ednspace/PyroLogger/Hardware/ds2760/ds2760/board.png

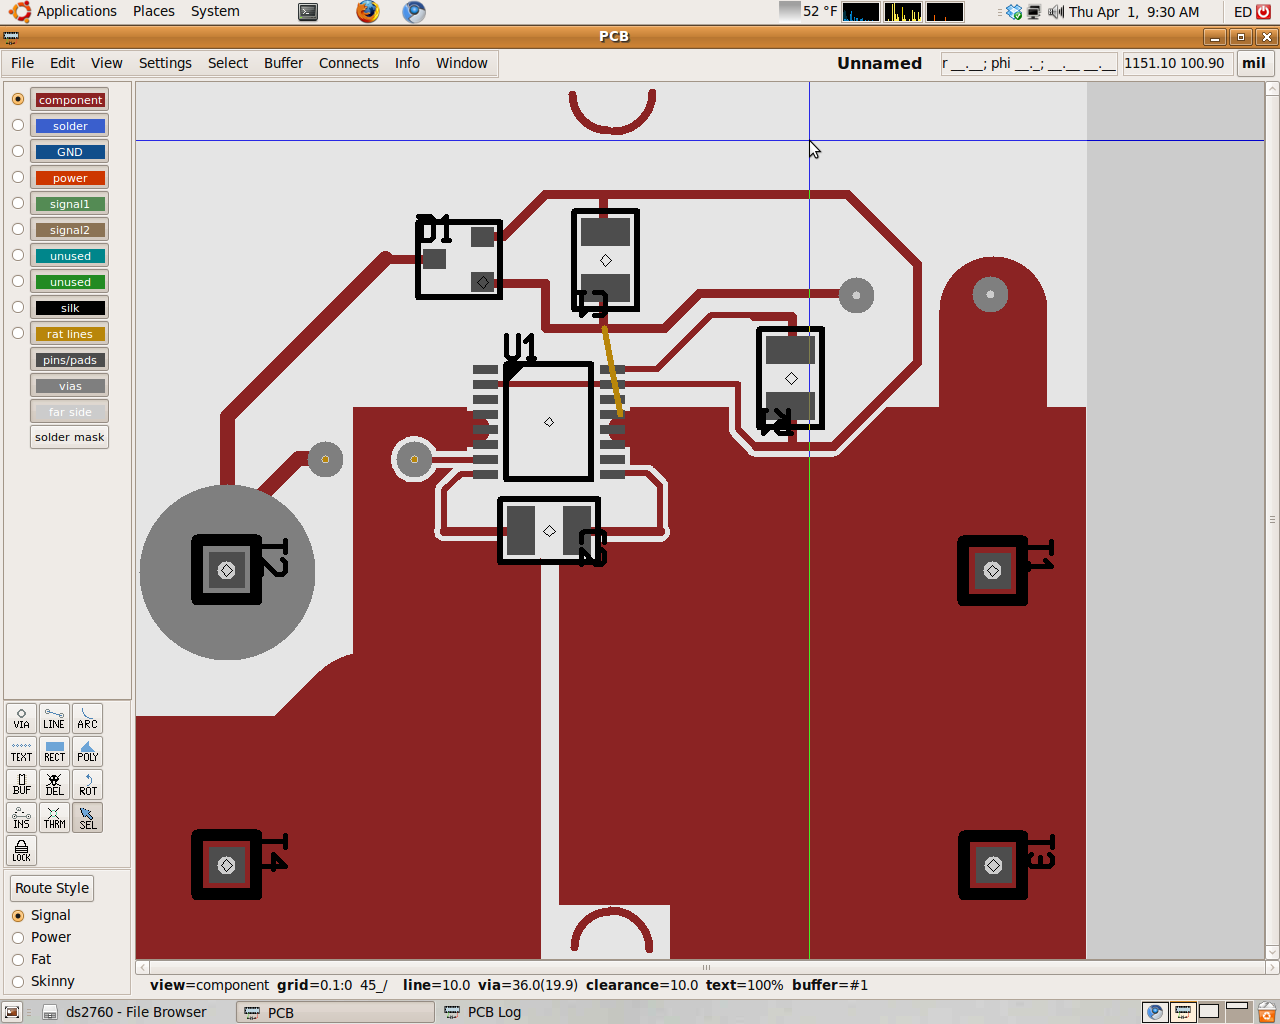
Hardware/ds2760/ds2760/board.png
