ednspace/PyroLogger/Hardware/FakeThermocouple/fake_scheme.JPG

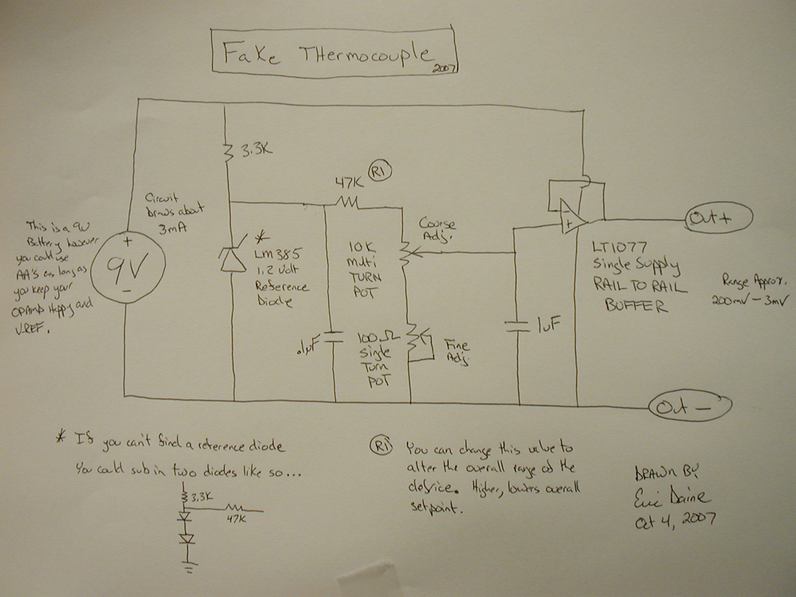
Hardware/FakeThermocouple/fake_scheme.JPG
