ednspace/PyroLogger/Images/2015-05-17 10.12.58.jpg

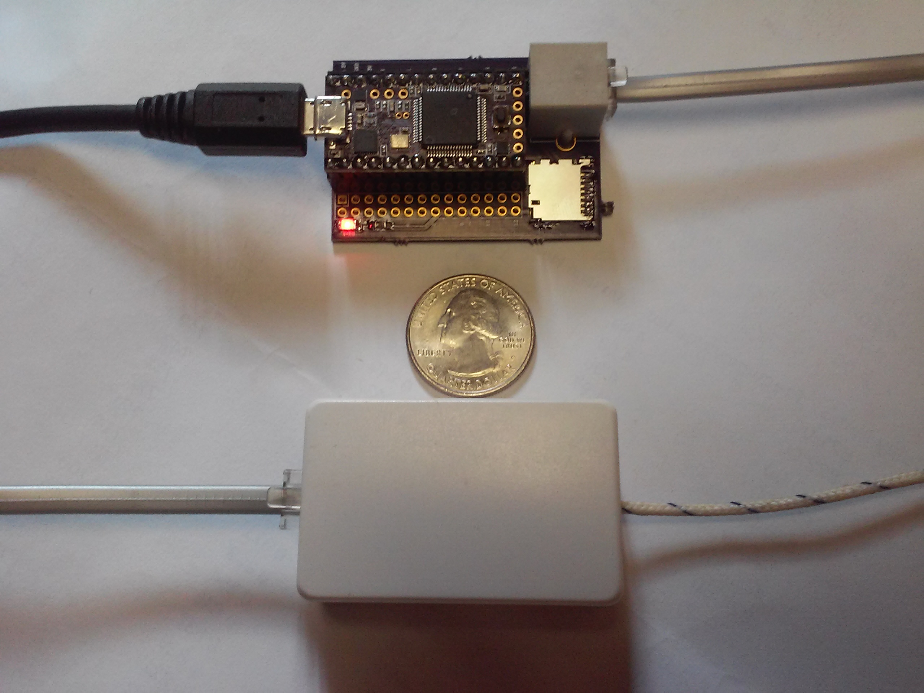
Images/2015-05-17 10.12.58.jpg
