ednspace/PyroLogger/Research/16F688_FT232RL.png

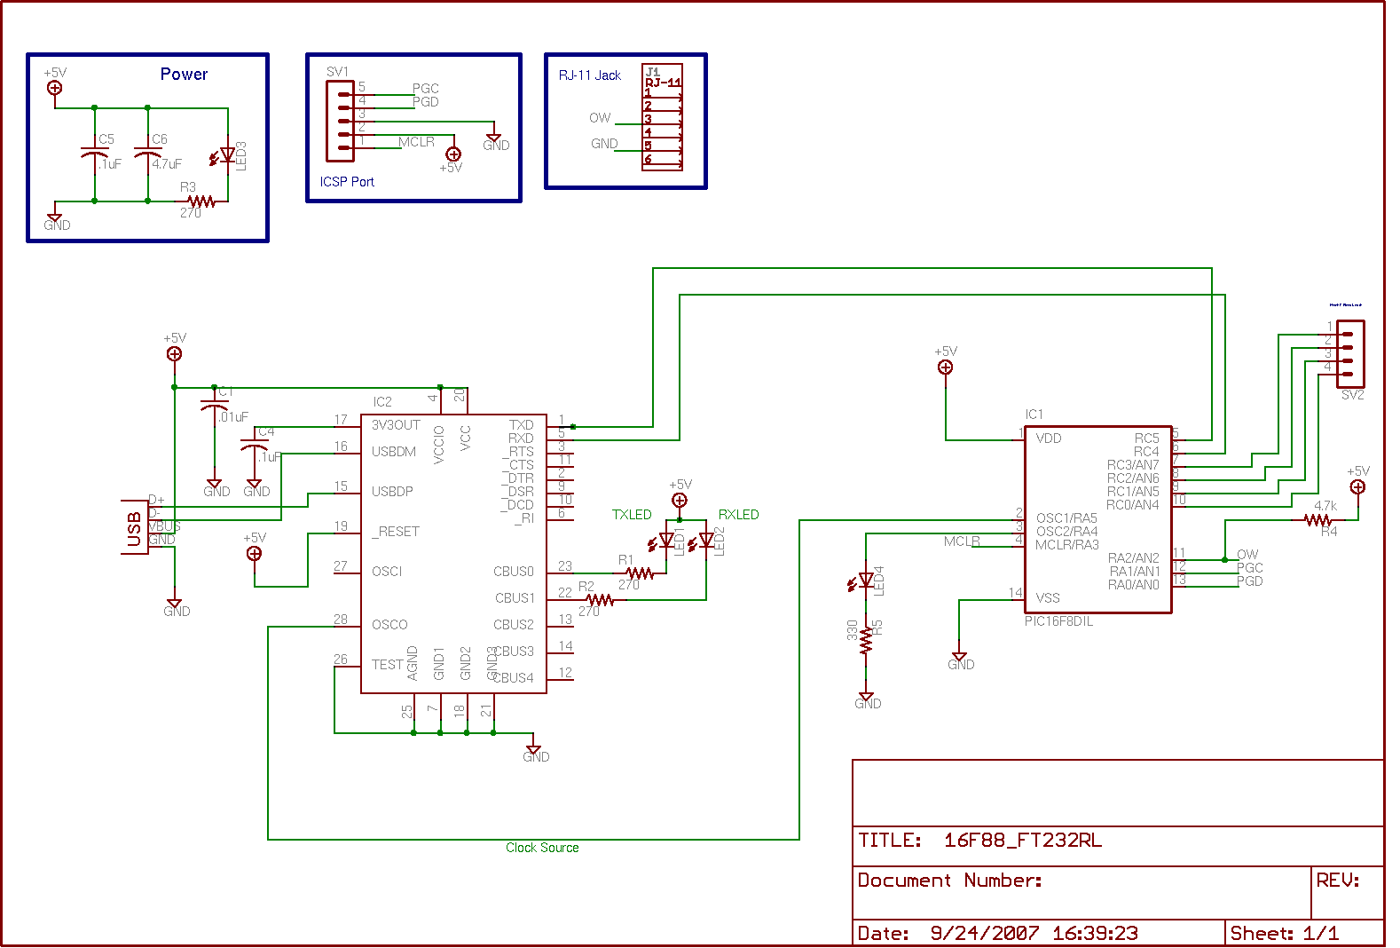
Research/16F688_FT232RL.png
