ednspace/PyroLogger/Research/ds2460.png

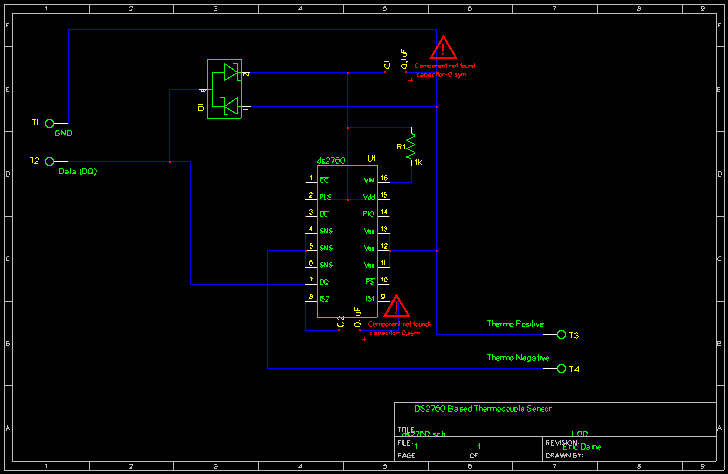
Research/ds2460.png
