ednspace/PyroLogger/Testing/Anagama_2006_oct/oct06.png

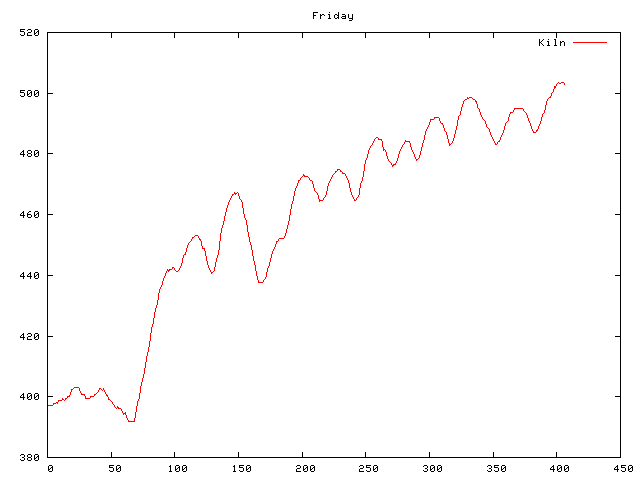
Testing/Anagama_2006_oct/oct06.png
