ednspace/PyroLogger/Testing/Anagama_2006_oct/oct07.png

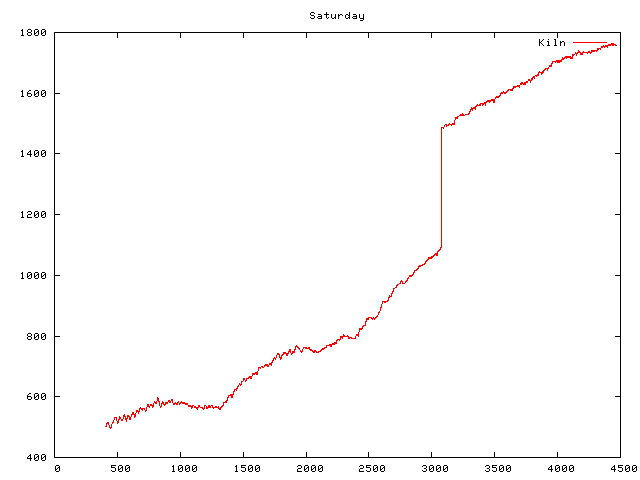
Testing/Anagama_2006_oct/oct07.png
