ednspace/PyroLogger/Testing/Anagama_2006_oct/oct08.png

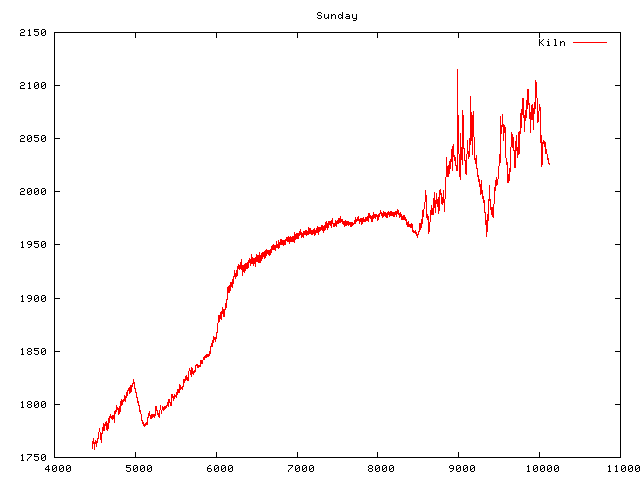
Testing/Anagama_2006_oct/oct08.png
