ednspace/PyroLogger/Testing/Anagama_2006_oct/oct09.png

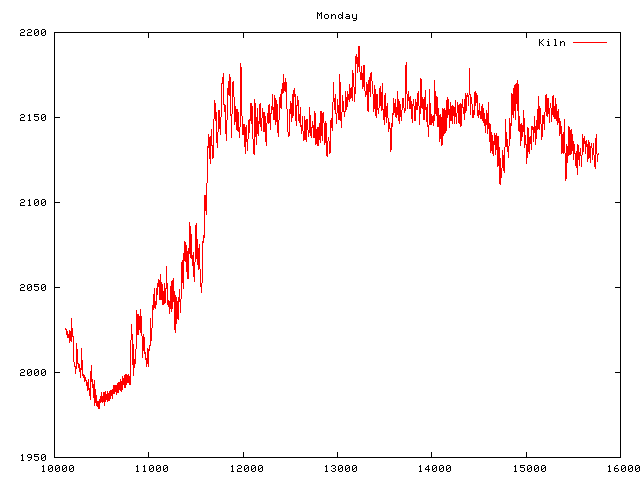
Testing/Anagama_2006_oct/oct09.png
