ednspace/PyroLogger/Testing/Anagama_2006_oct/oct10.png

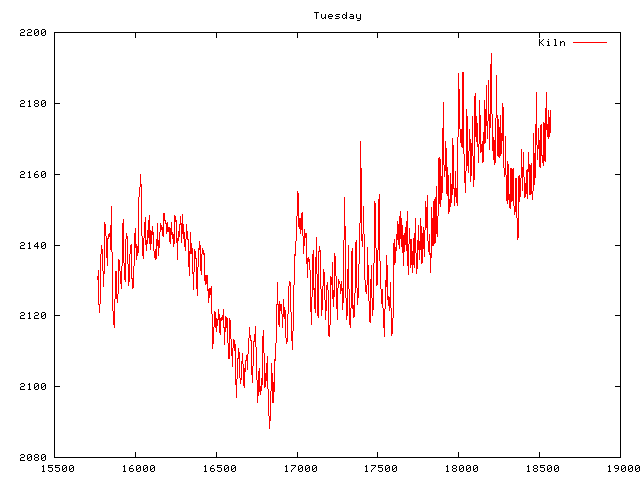
Testing/Anagama_2006_oct/oct10.png
