ednspace/PyroLogger/Testing/Anagama_2006_oct/Thumbs/whole.png

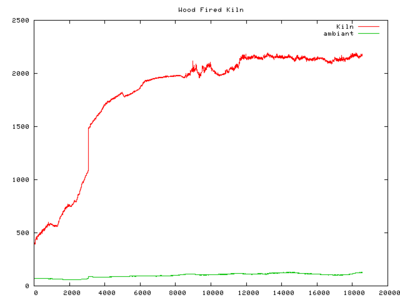
Testing/Anagama_2006_oct/Thumbs/whole.png
