ednspace/PyroLogger/Testing/Anagama_2007_march/march06.png

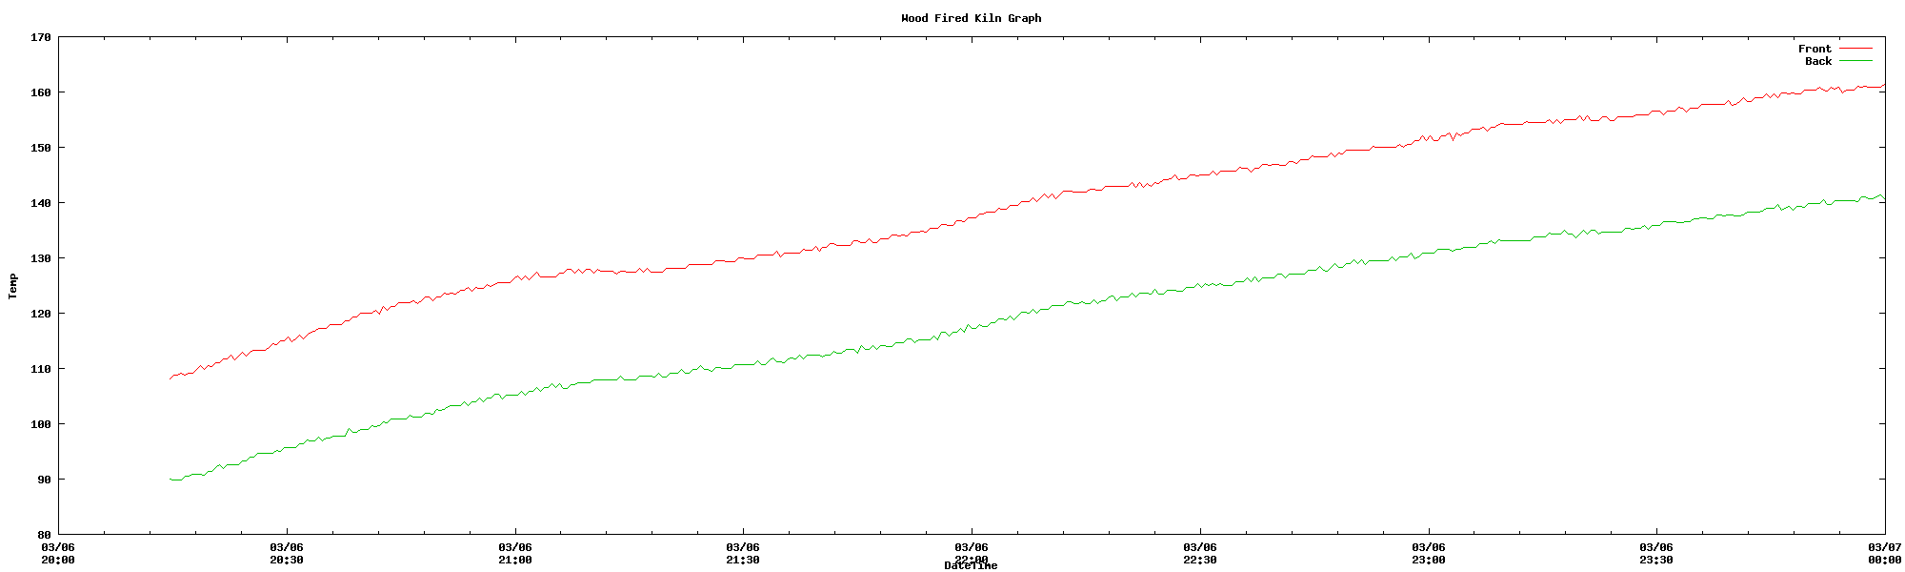
Testing/Anagama_2007_march/march06.png
