ednspace/PyroLogger/Testing/Anagama_2007_march/march07.png

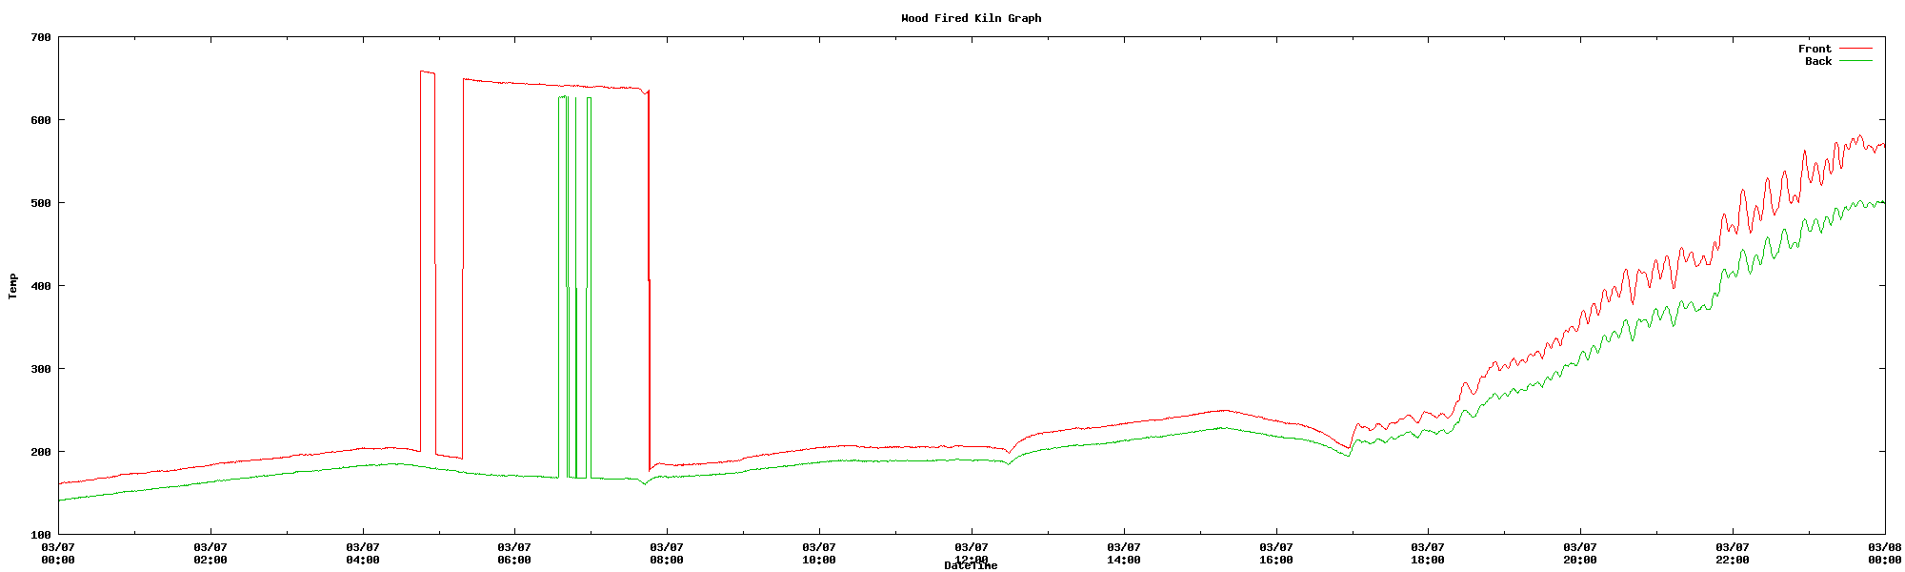
Testing/Anagama_2007_march/march07.png
