ednspace/PyroLogger/Testing/Anagama_2007_march/march08.png

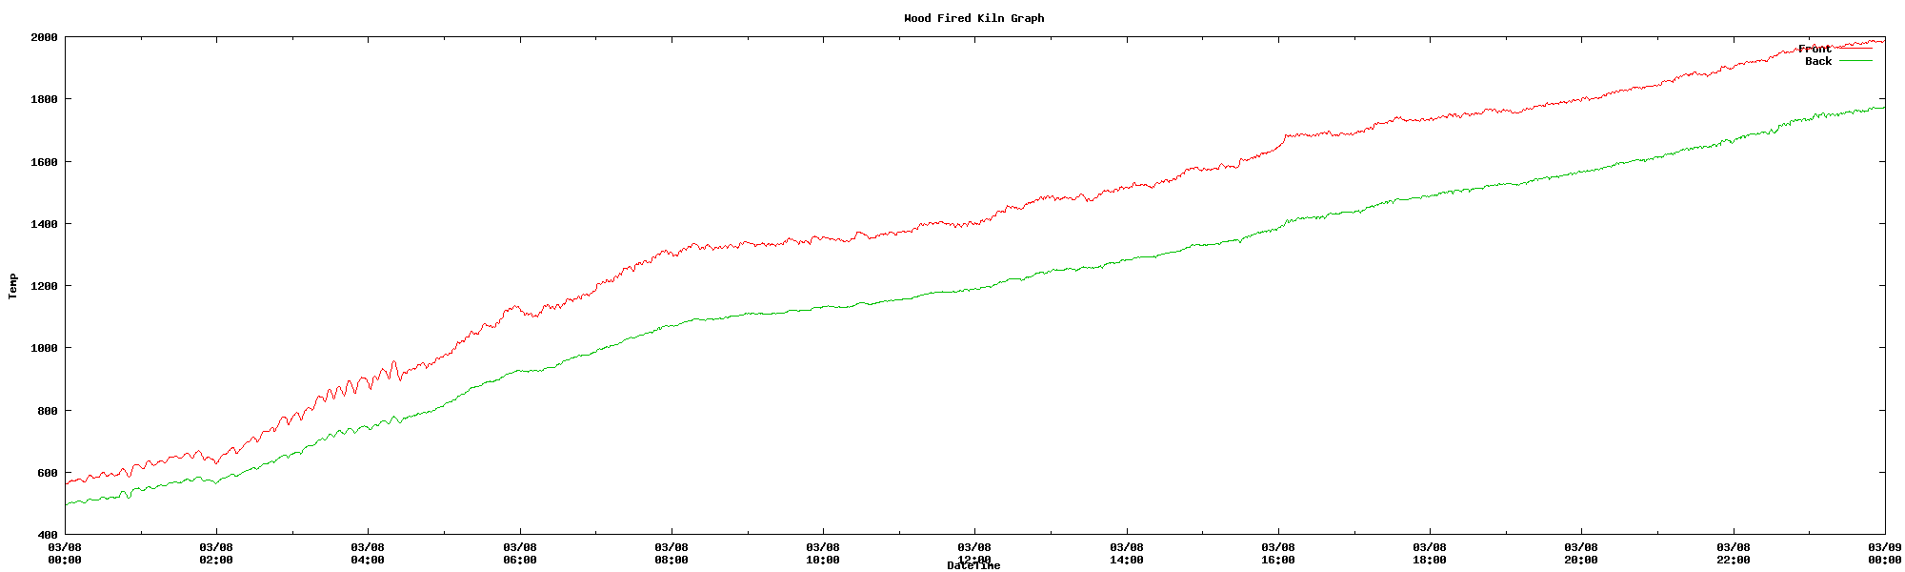
Testing/Anagama_2007_march/march08.png
