ednspace/PyroLogger/Testing/Anagama_2007_march/march09.png

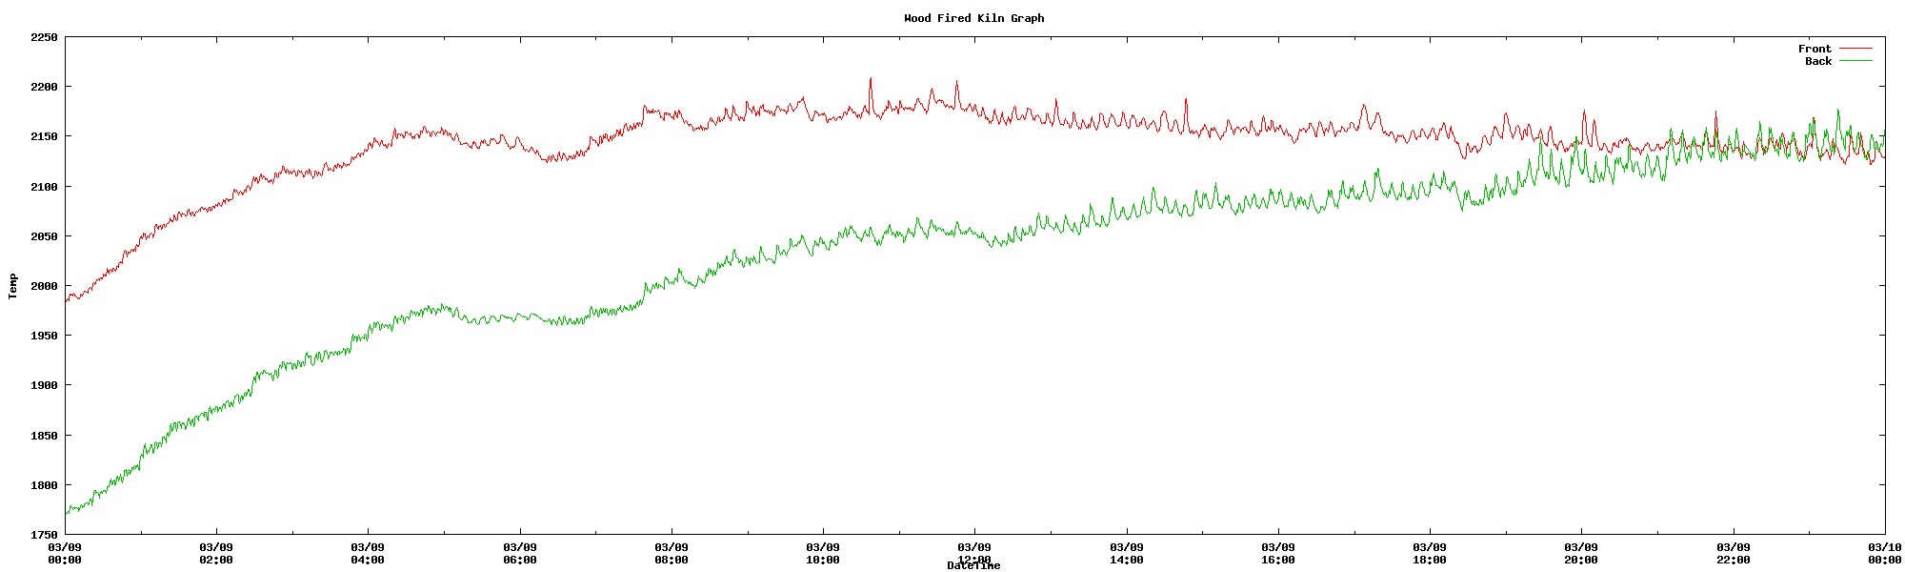
Testing/Anagama_2007_march/march09.png
