ednspace/PyroLogger/Testing/Anagama_2007_march/march10.png

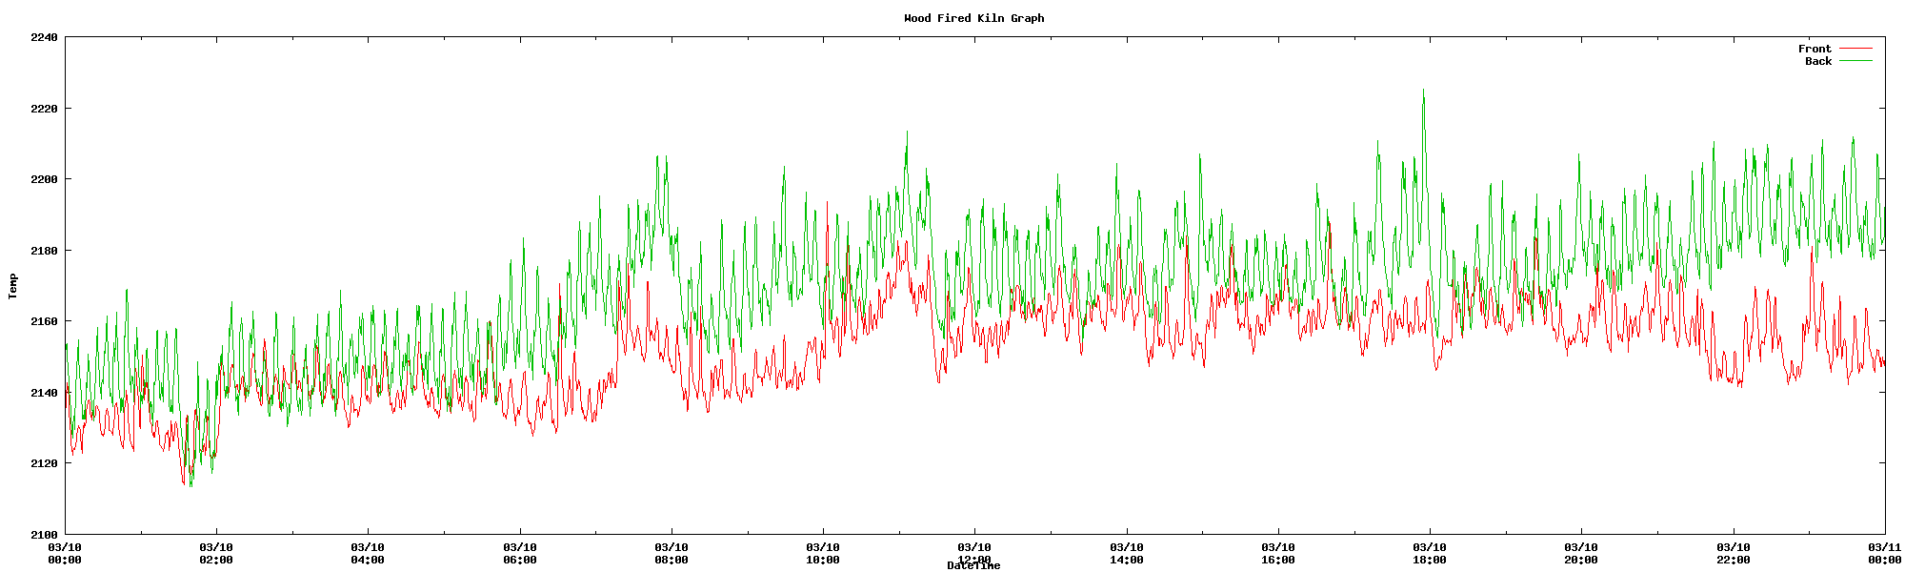
Testing/Anagama_2007_march/march10.png
