ednspace/PyroLogger/Testing/Anagama_2007_march/march11.png

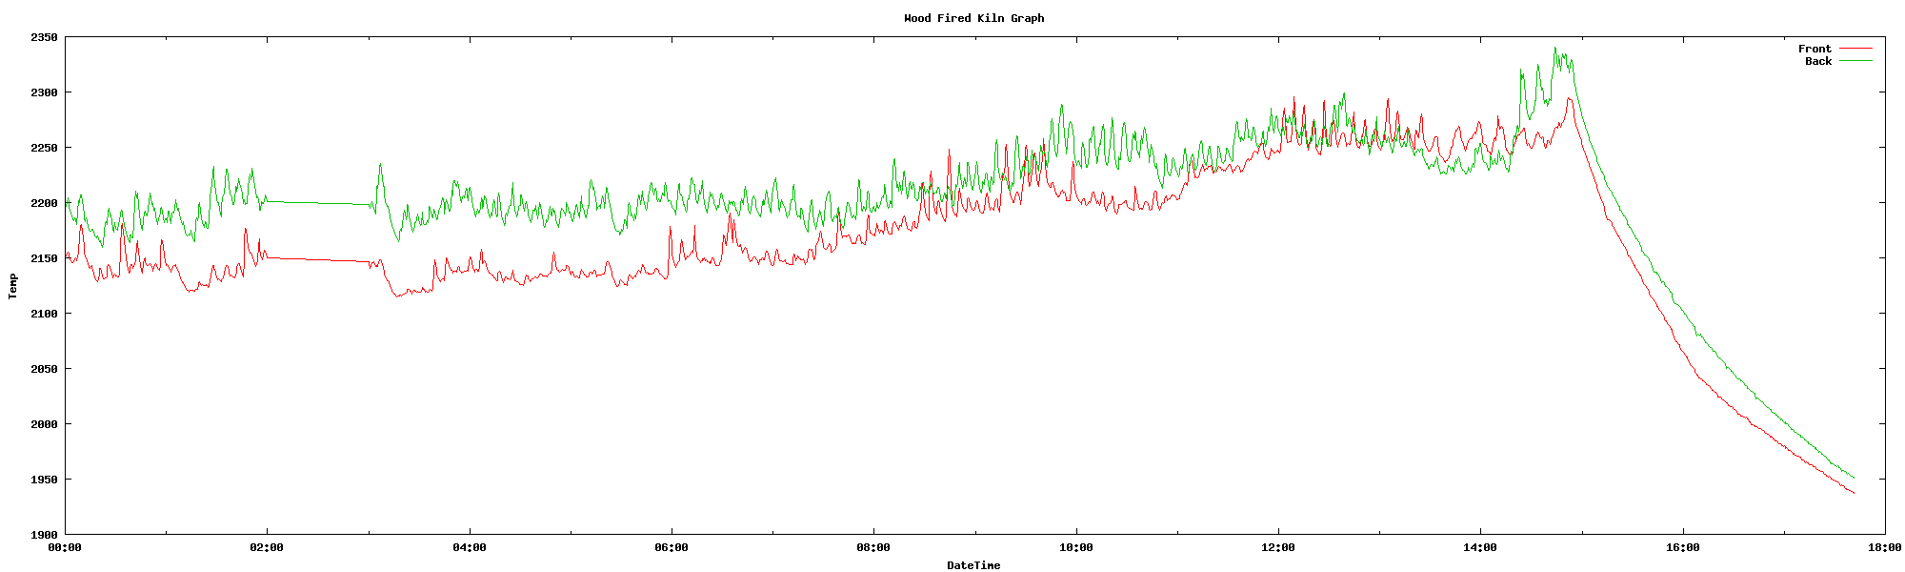
Testing/Anagama_2007_march/march11.png
