ednspace/PyroLogger/Testing/Anagama_2007_march/Thumbs/march06.png

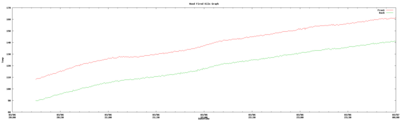
Testing/Anagama_2007_march/Thumbs/march06.png
