ednspace/PyroLogger/Testing/Anagama_2007_march/Thumbs/whole_graph.png

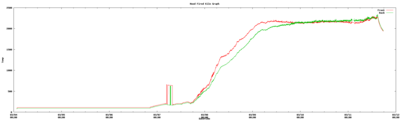
Testing/Anagama_2007_march/Thumbs/whole_graph.png
