ednspace/PyroLogger/Testing/Anagama_2007_oct/oct05.png

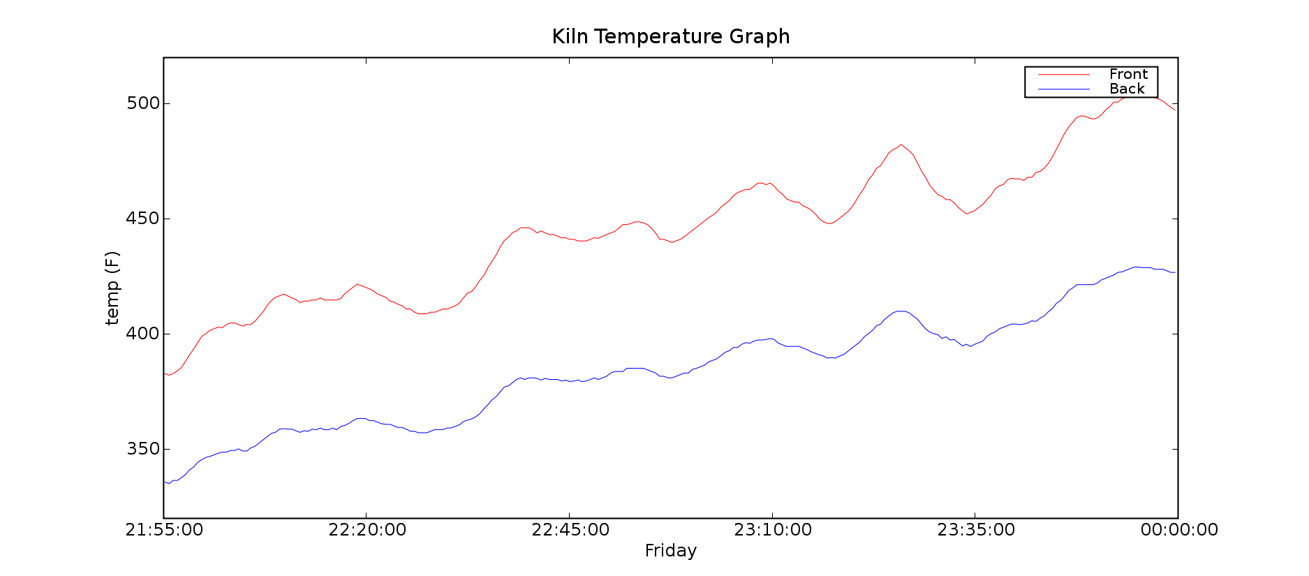
Testing/Anagama_2007_oct/oct05.png
