ednspace/PyroLogger/Testing/Anagama_2007_oct/oct06.png

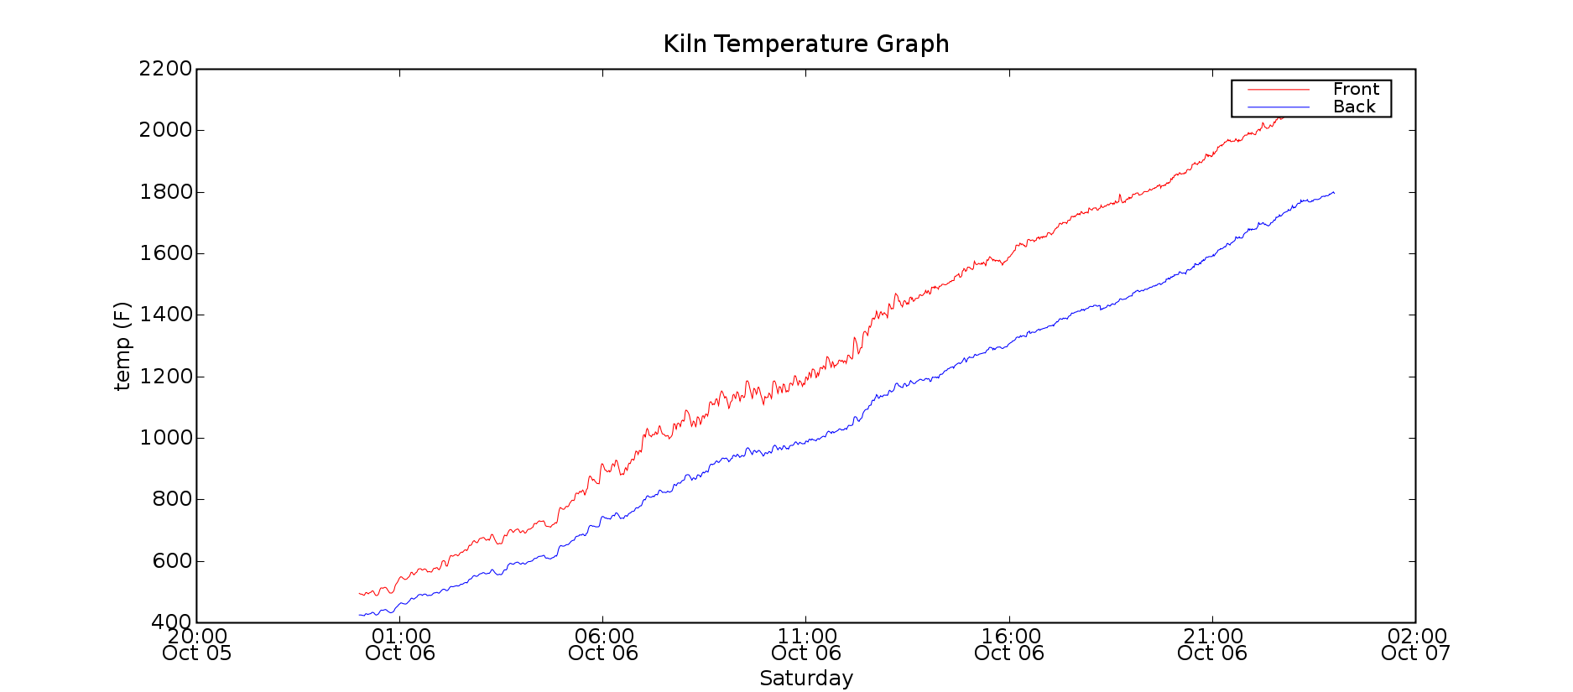
Testing/Anagama_2007_oct/oct06.png
