ednspace/PyroLogger/Testing/Anagama_2007_oct/oct07.png

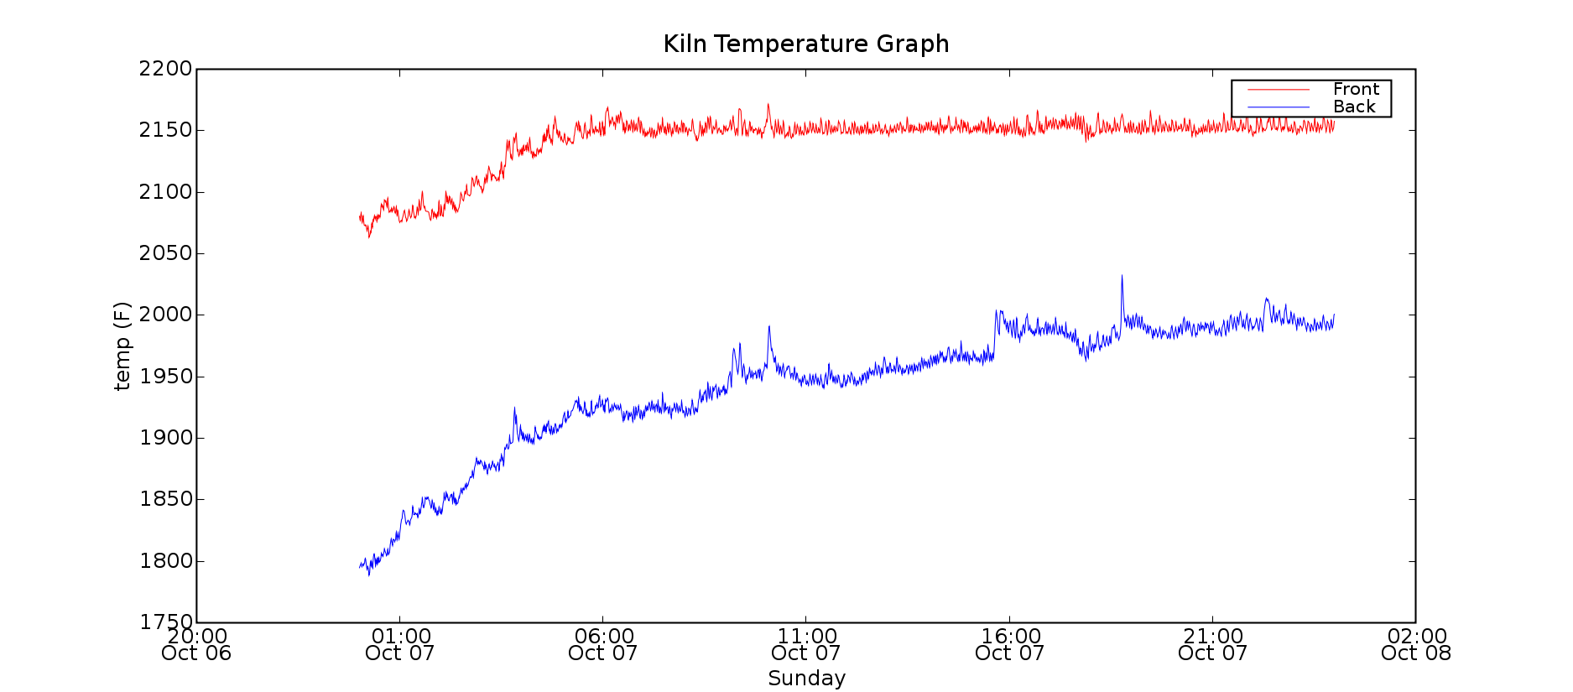
Testing/Anagama_2007_oct/oct07.png
