ednspace/PyroLogger/Testing/Anagama_2007_oct/oct08.png

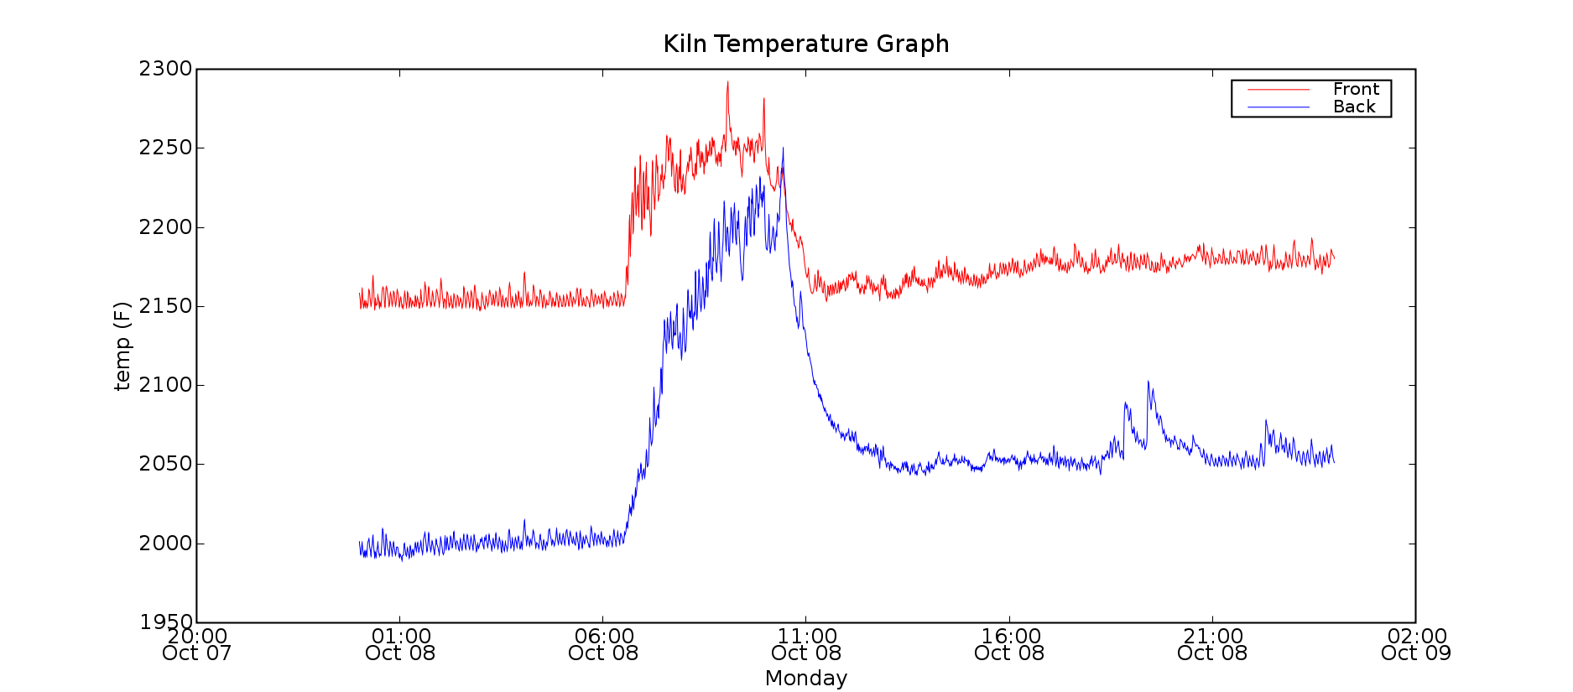
Testing/Anagama_2007_oct/oct08.png
