ednspace/PyroLogger/Testing/Anagama_2007_oct/oct09.png

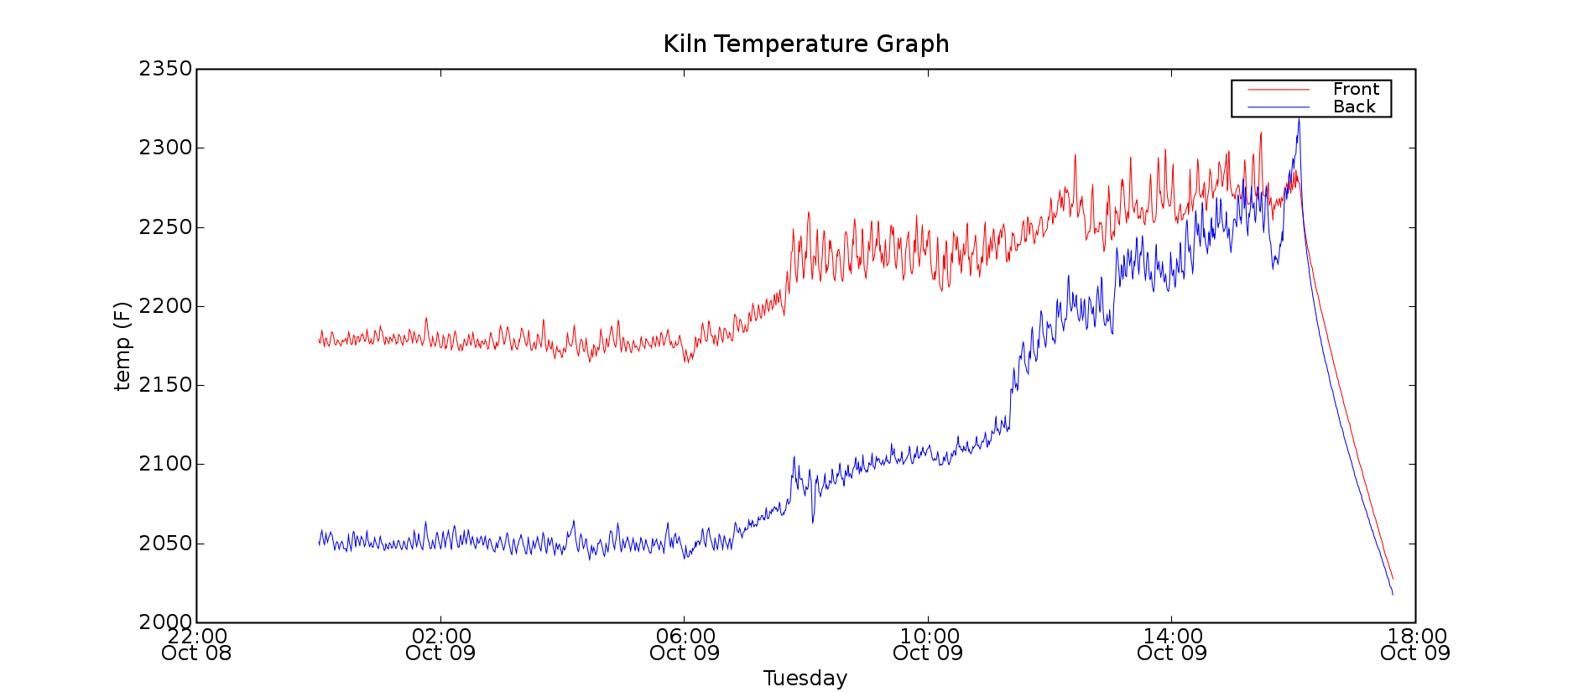
Testing/Anagama_2007_oct/oct09.png
