ednspace/PyroLogger/Testing/Anagama_2007_oct/Thumbs/oct08.png

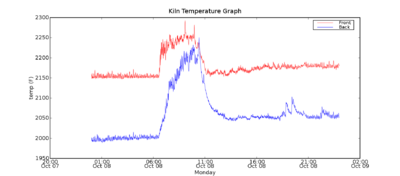
Testing/Anagama_2007_oct/Thumbs/oct08.png
