ednspace/PyroLogger/Testing/Anagama_2007_oct/Thumbs/whole.png

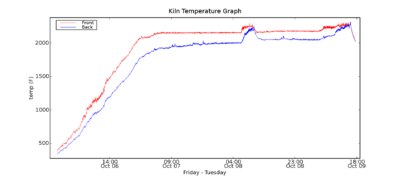
Testing/Anagama_2007_oct/Thumbs/whole.png
