ednspace/PyroLogger/Testing/Anagama_2009_april/day1.png

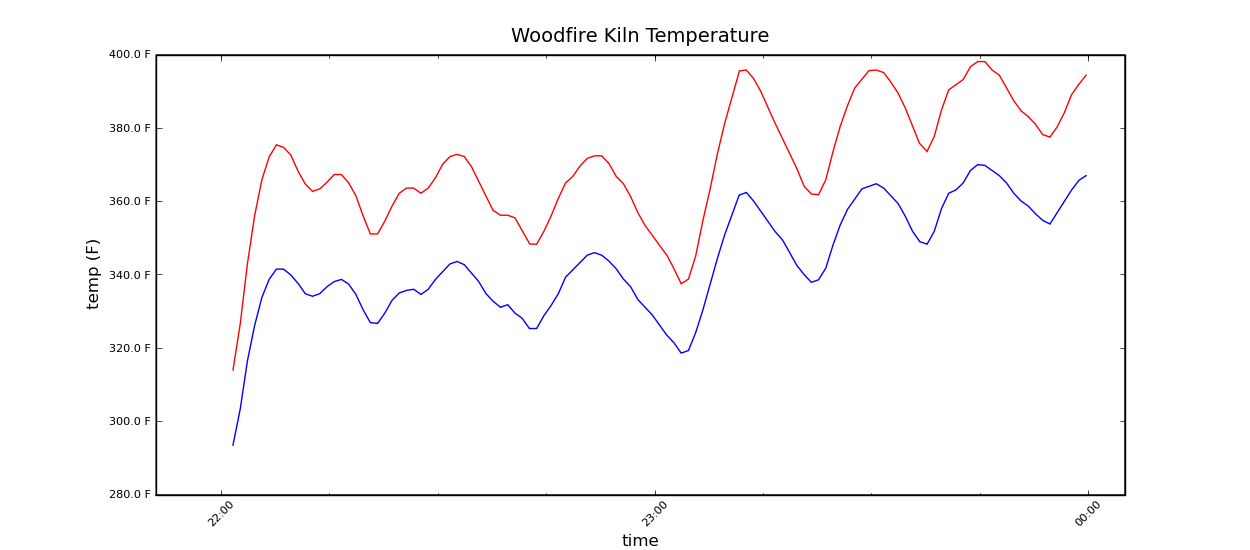
Testing/Anagama_2009_april/day1.png
