ednspace/PyroLogger/Testing/Anagama_2009_april/day2.png

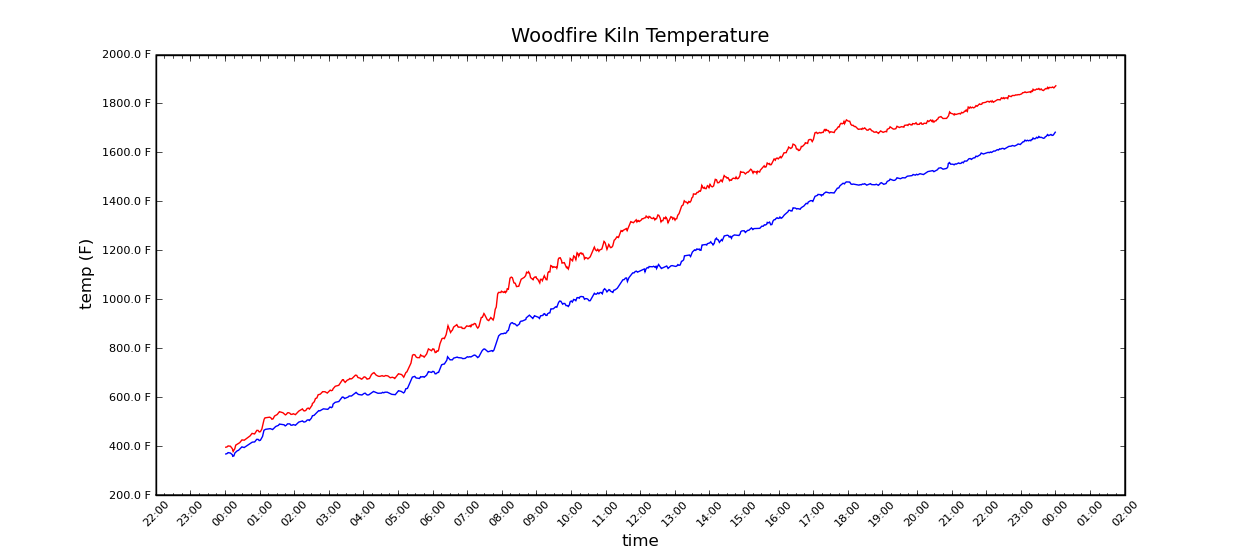
Testing/Anagama_2009_april/day2.png
