ednspace/PyroLogger/Testing/Anagama_2009_april/day3.png

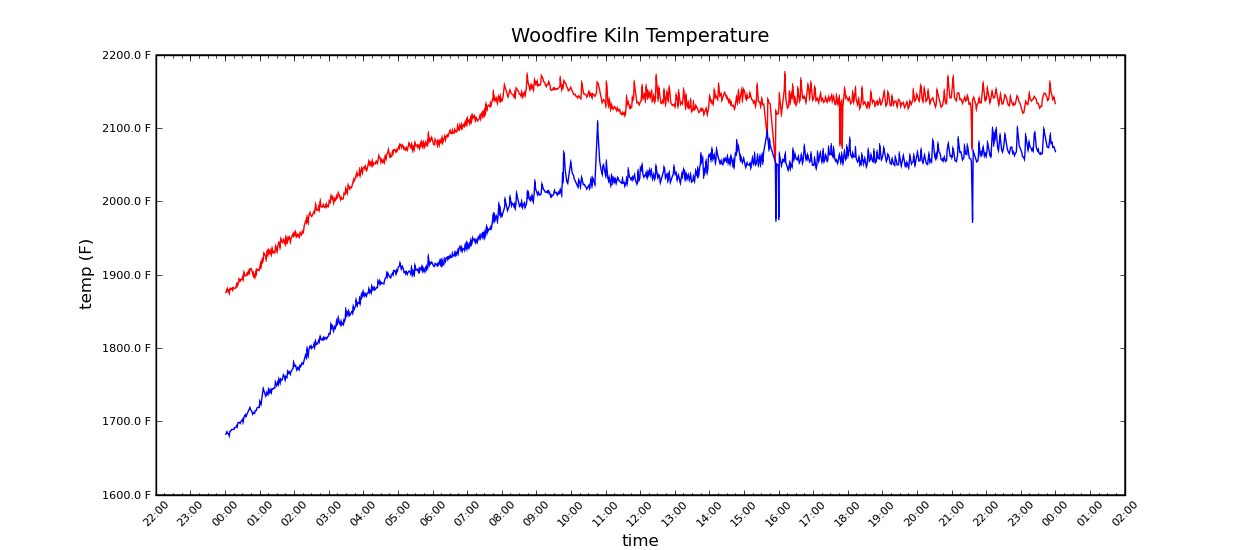
Testing/Anagama_2009_april/day3.png
