ednspace/PyroLogger/Testing/Anagama_2009_april/day4.png

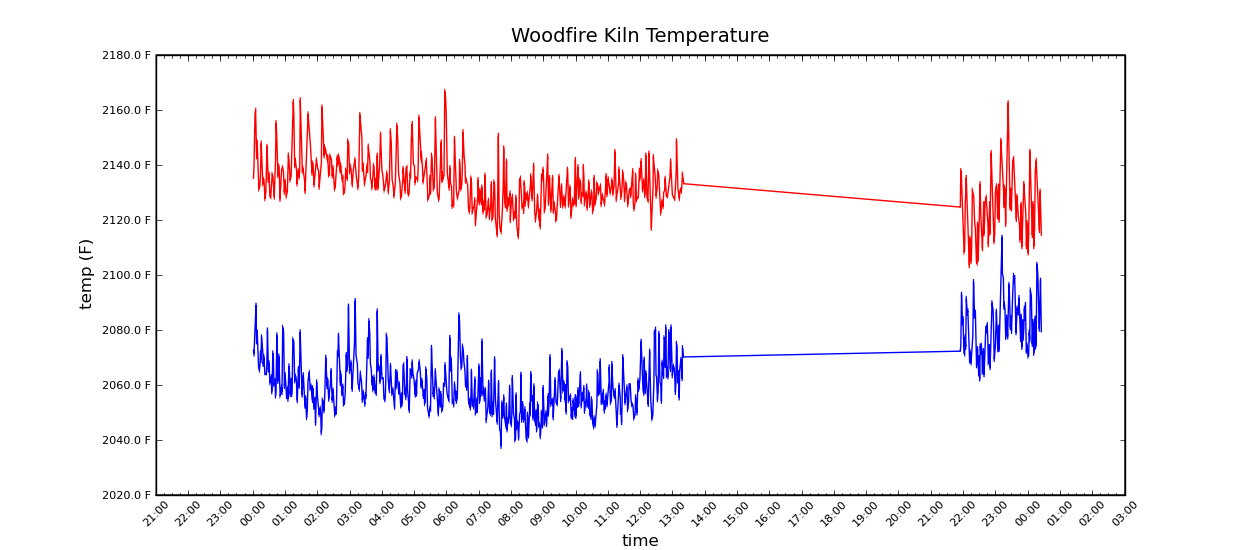
Testing/Anagama_2009_april/day4.png
