ednspace/PyroLogger/Testing/Anagama_2009_april/Thumbs/whole.png

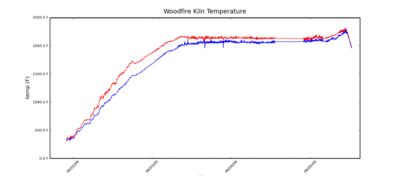
Testing/Anagama_2009_april/Thumbs/whole.png
