ednspace/PyroLogger/Testing/Anagama_2009_nov/day1.png

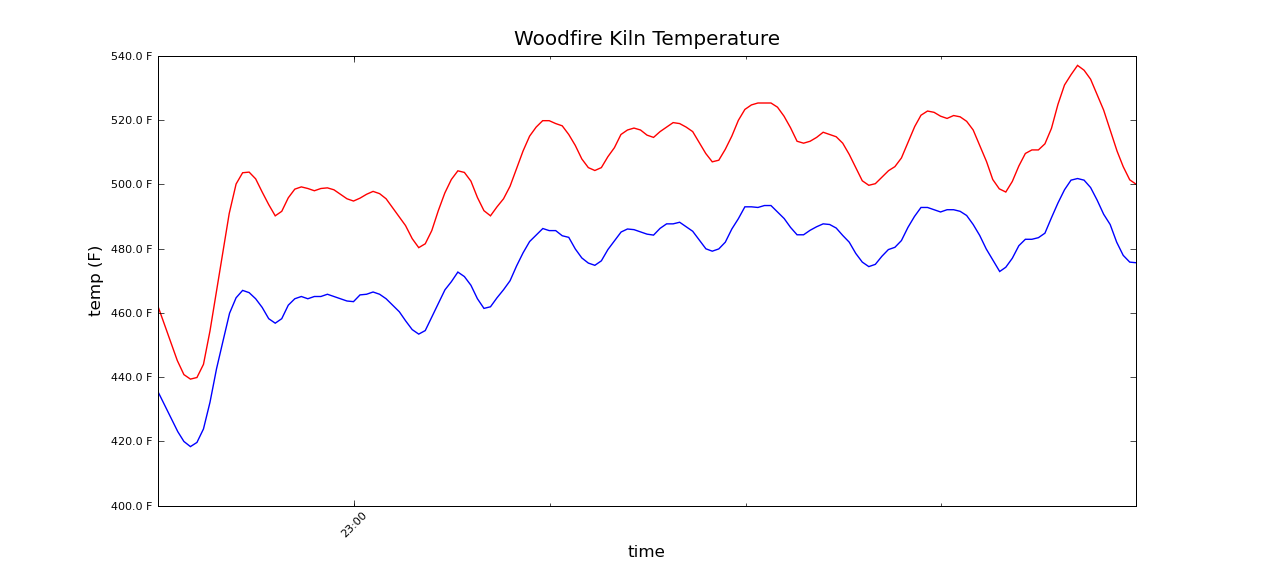
Testing/Anagama_2009_nov/day1.png
