ednspace/PyroLogger/Testing/Anagama_2009_nov/day2.png

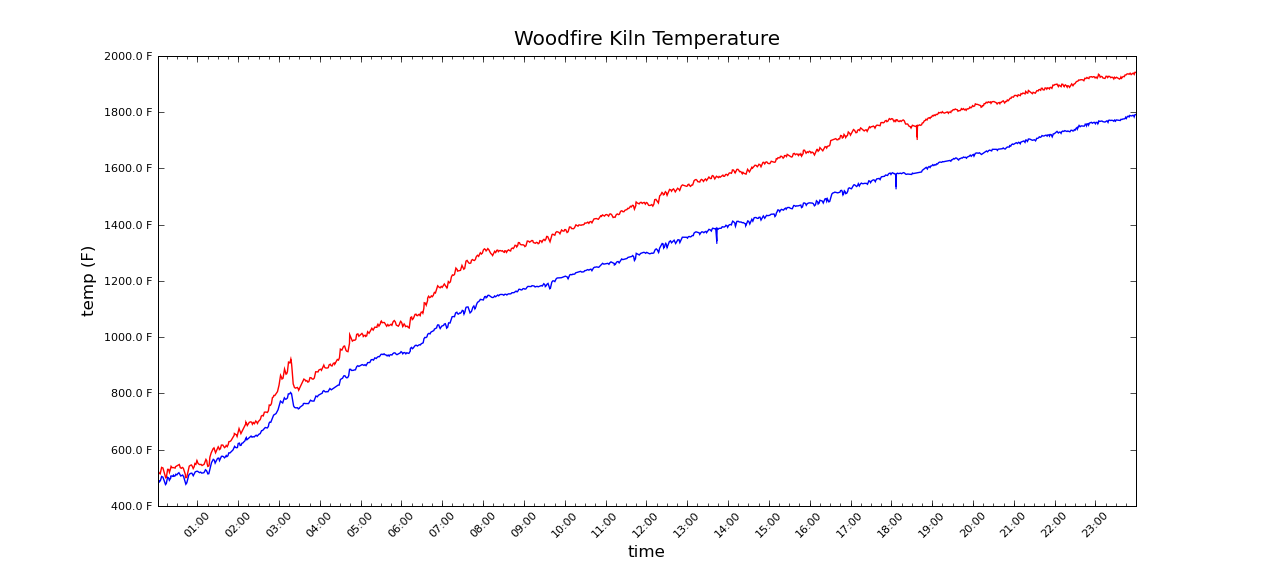
Testing/Anagama_2009_nov/day2.png
