ednspace/PyroLogger/Testing/Anagama_2009_nov/day3.png

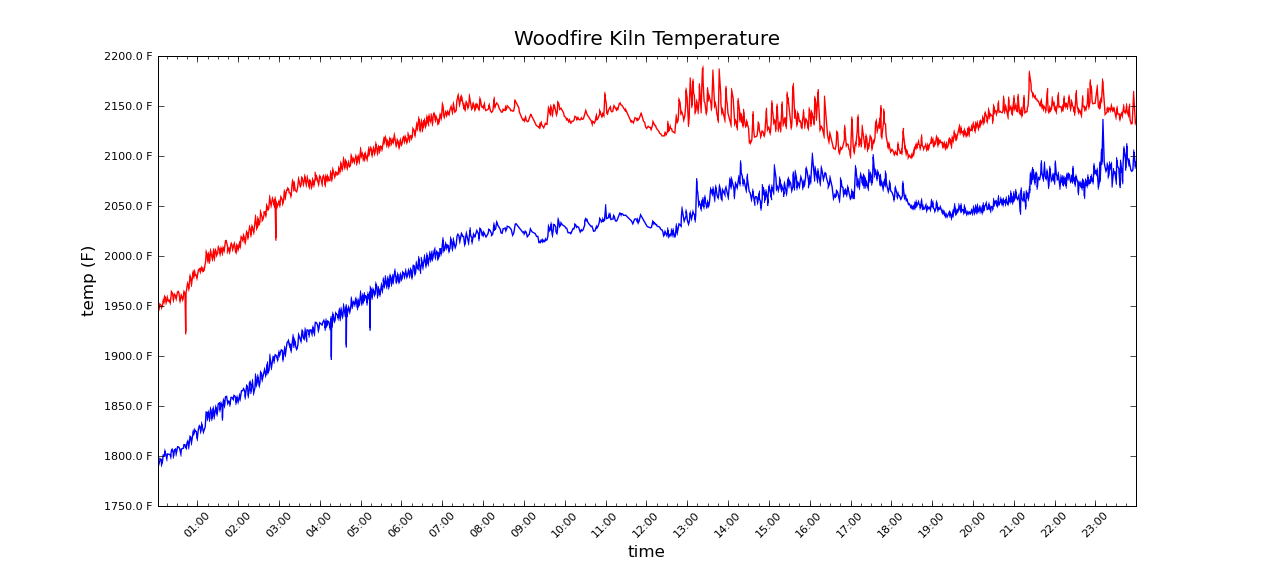
Testing/Anagama_2009_nov/day3.png
