ednspace/PyroLogger/Testing/Anagama_2009_nov/day4.png

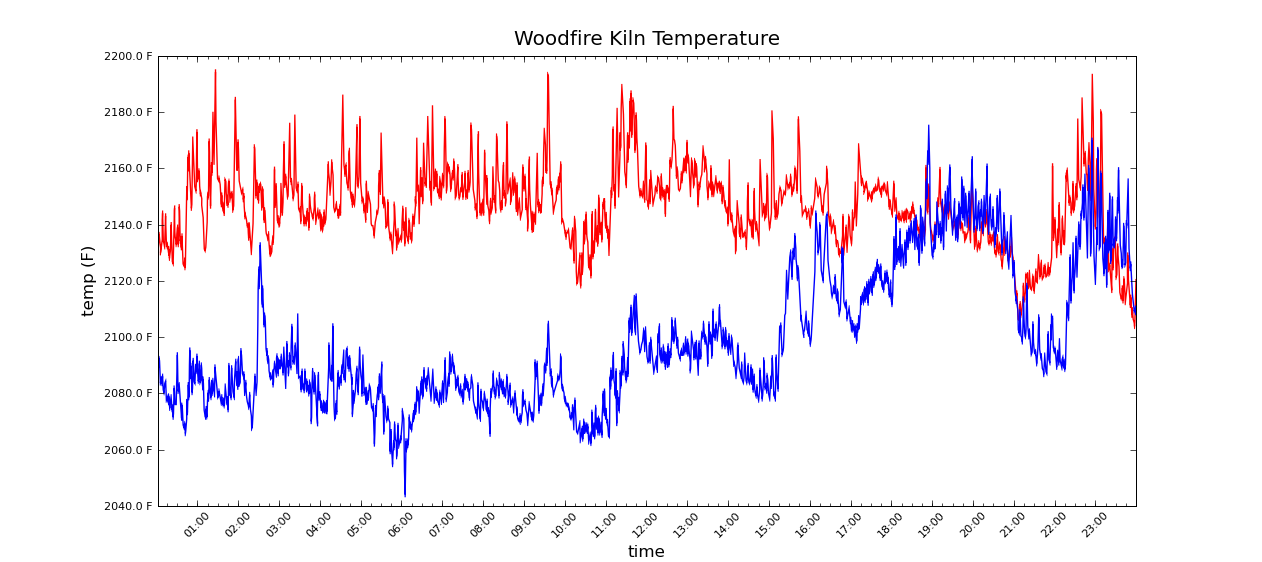
Testing/Anagama_2009_nov/day4.png
