ednspace/PyroLogger/Testing/Anagama_2009_nov/day5.png

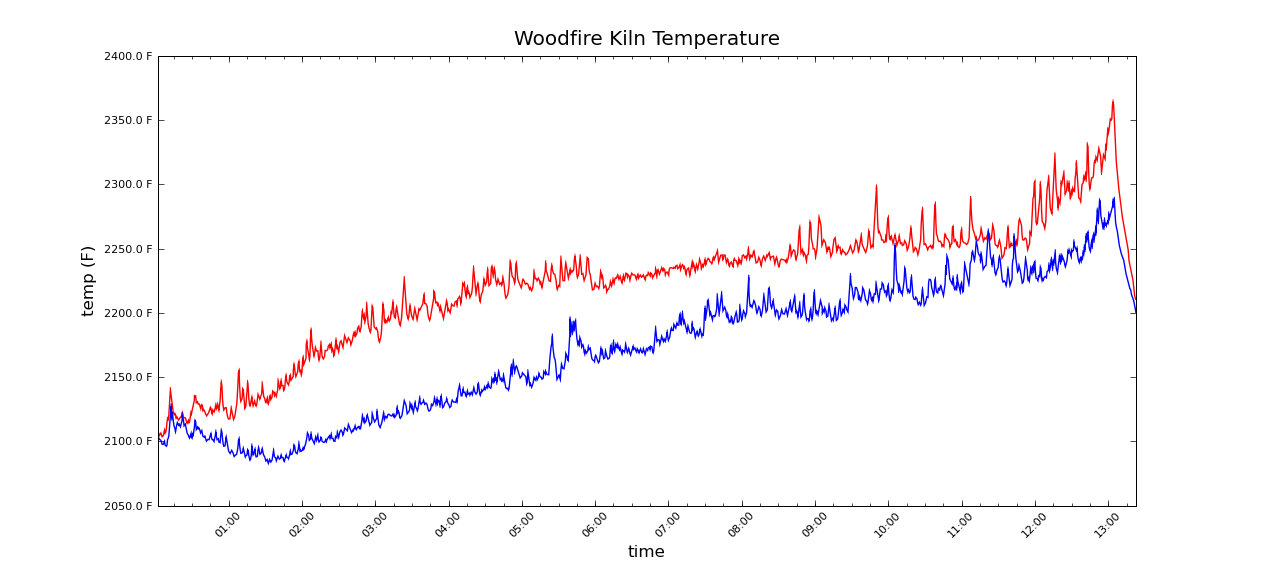
Testing/Anagama_2009_nov/day5.png
