ednspace/PyroLogger/Testing/Anagama_2009_nov/thumbs/whole.png

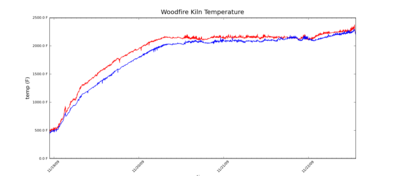
Testing/Anagama_2009_nov/thumbs/whole.png
