ednspace/PyroLogger/Testing/Anagama_2010_april/day1.png

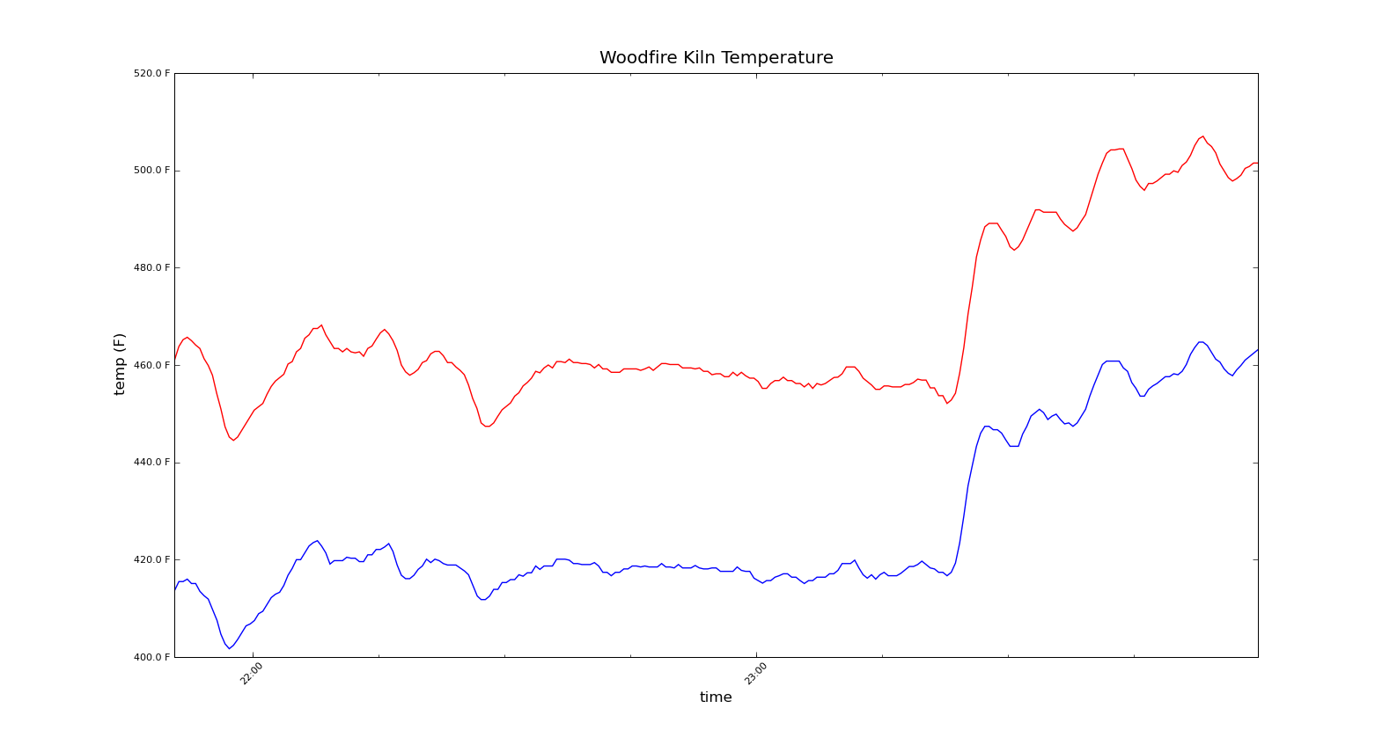
Testing/Anagama_2010_april/day1.png
