ednspace/PyroLogger/Testing/Anagama_2010_april/day3.png

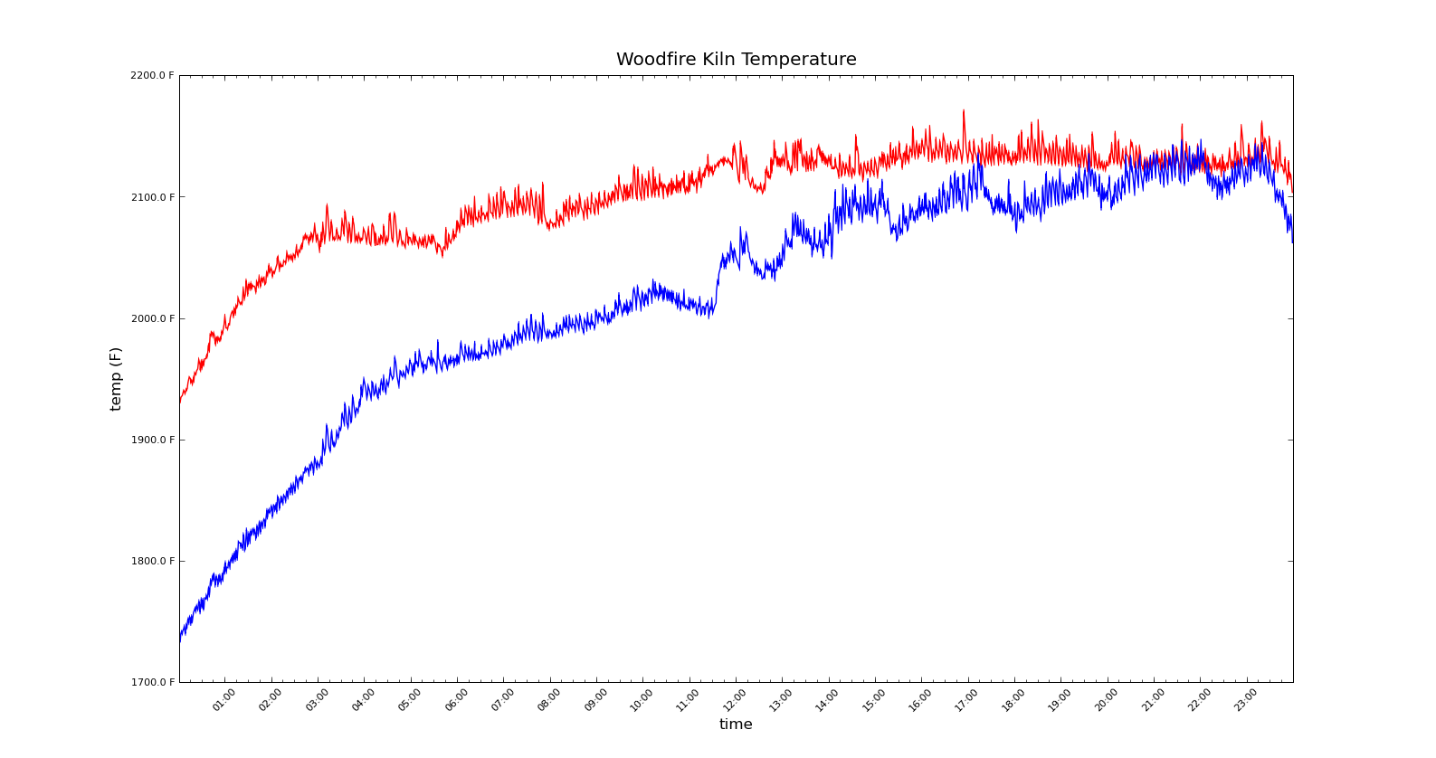
Testing/Anagama_2010_april/day3.png
