ednspace/PyroLogger/Testing/Anagama_2010_april/day4.png

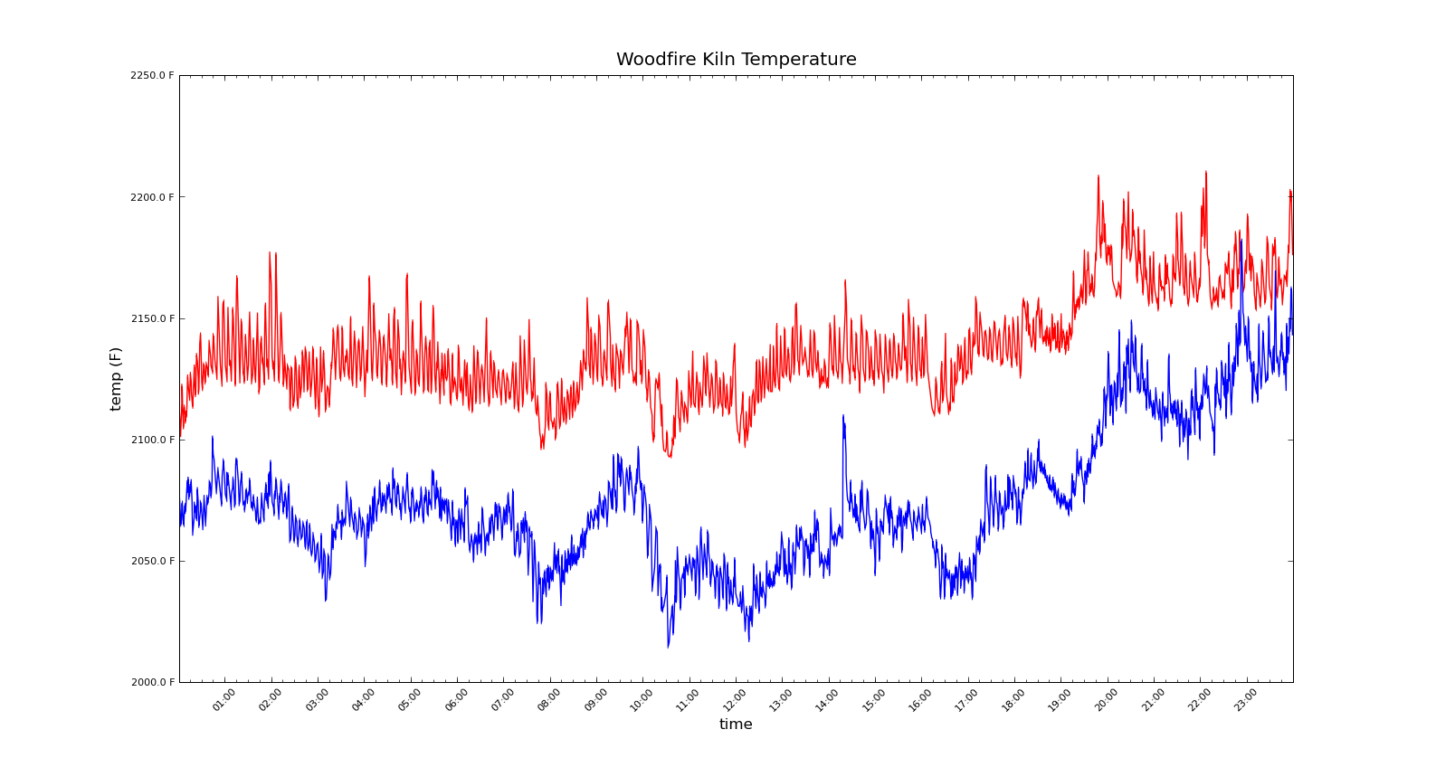
Testing/Anagama_2010_april/day4.png
