ednspace/PyroLogger/Testing/Anagama_2010_april/day5.png

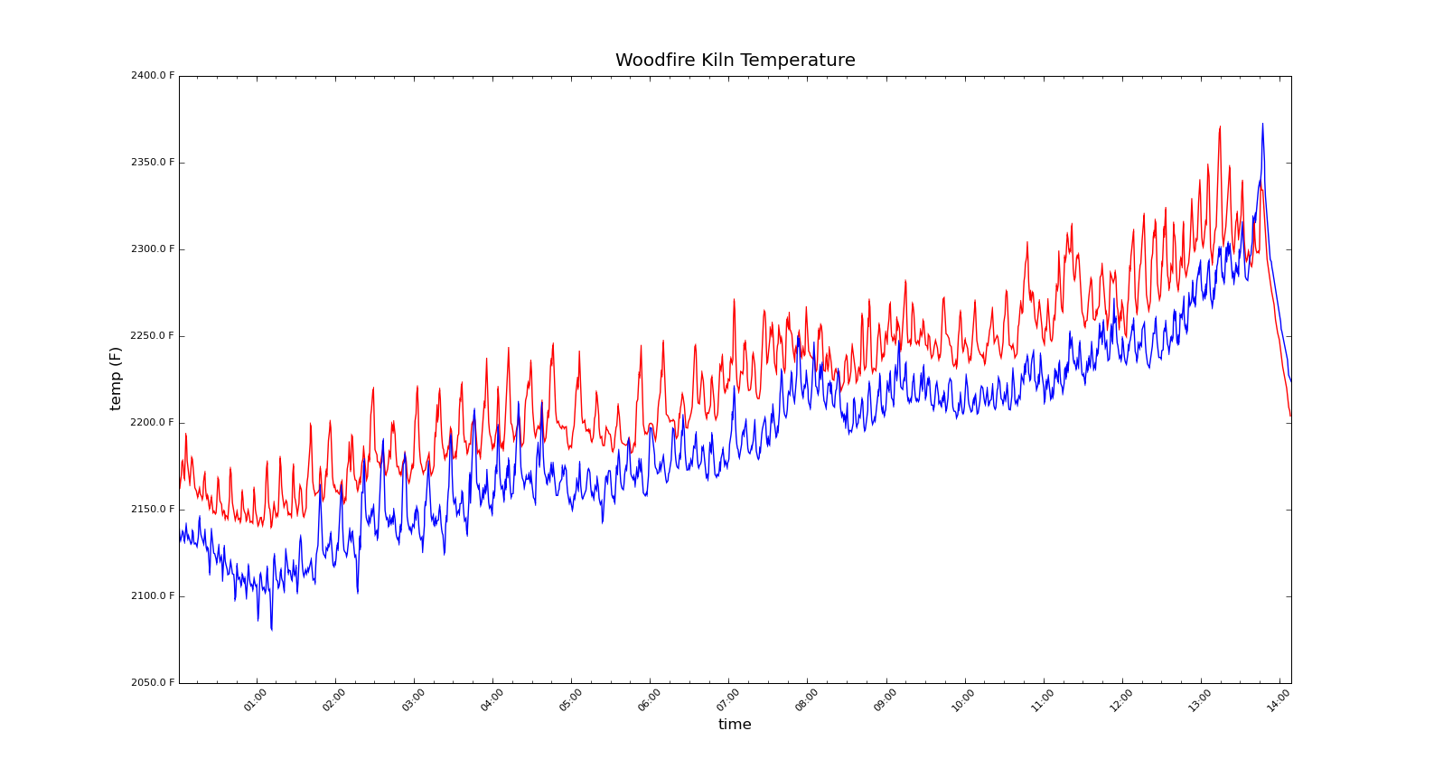
Testing/Anagama_2010_april/day5.png
