ednspace/PyroLogger/Testing/Anagama_2010_april/thumbs/whole.png

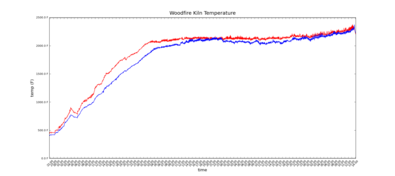
Testing/Anagama_2010_april/thumbs/whole.png
