ednspace/PyroLogger/Testing/Anagama_2010_april/whole.png

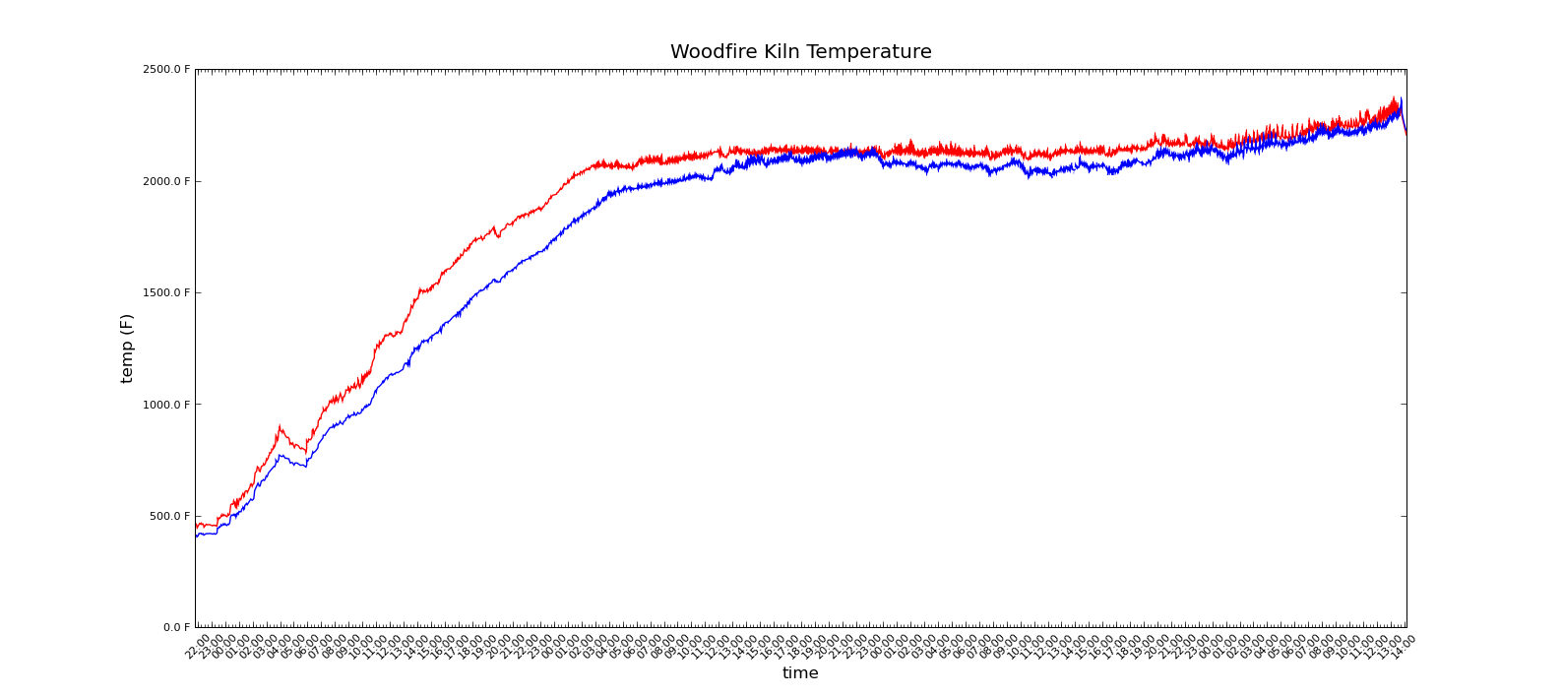
Testing/Anagama_2010_april/whole.png
