ednspace/PyroLogger/Testing/Anagama_2010_oct/day1.png

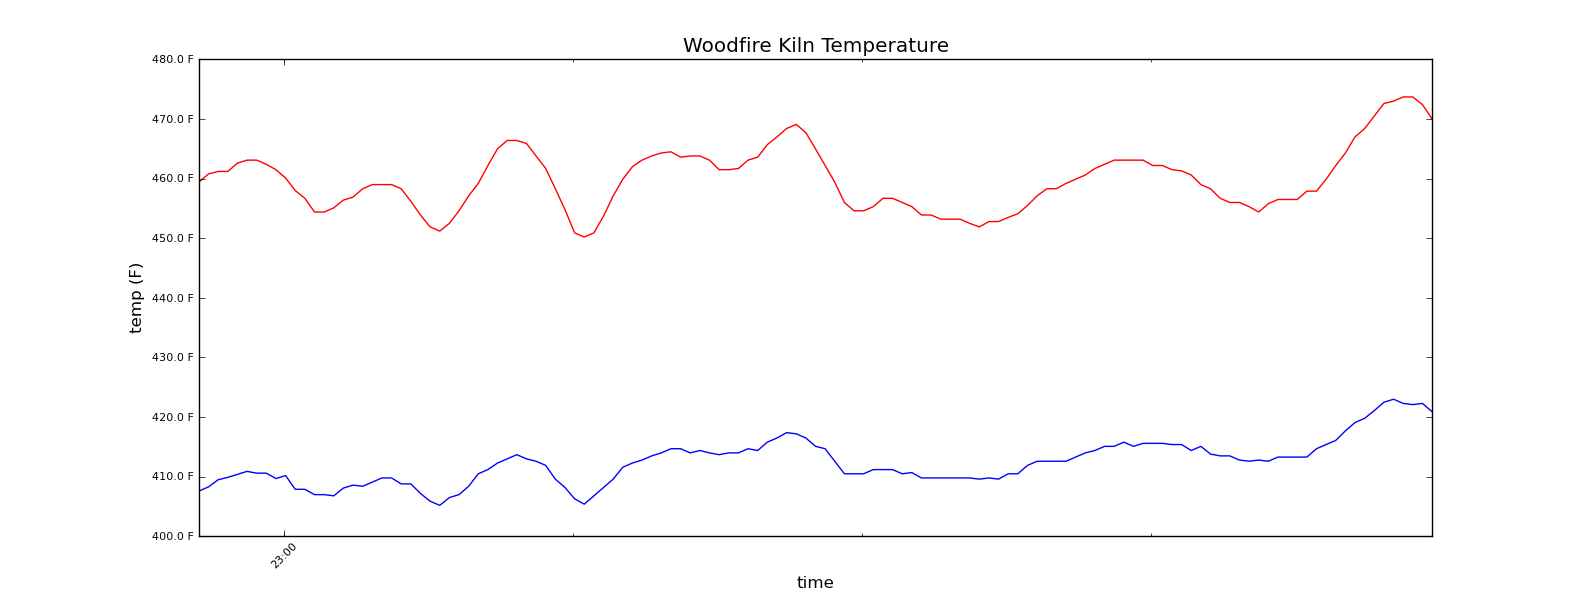
Testing/Anagama_2010_oct/day1.png
