ednspace/PyroLogger/Testing/Anagama_2010_oct/day2.png

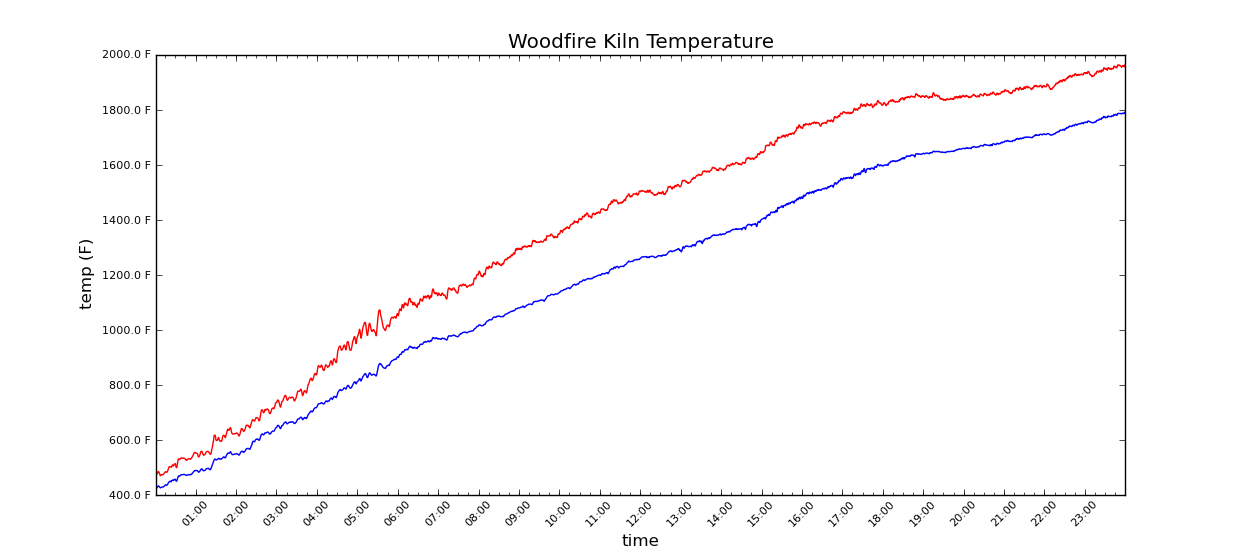
Testing/Anagama_2010_oct/day2.png
