ednspace/PyroLogger/Testing/Anagama_2010_oct/day3.png

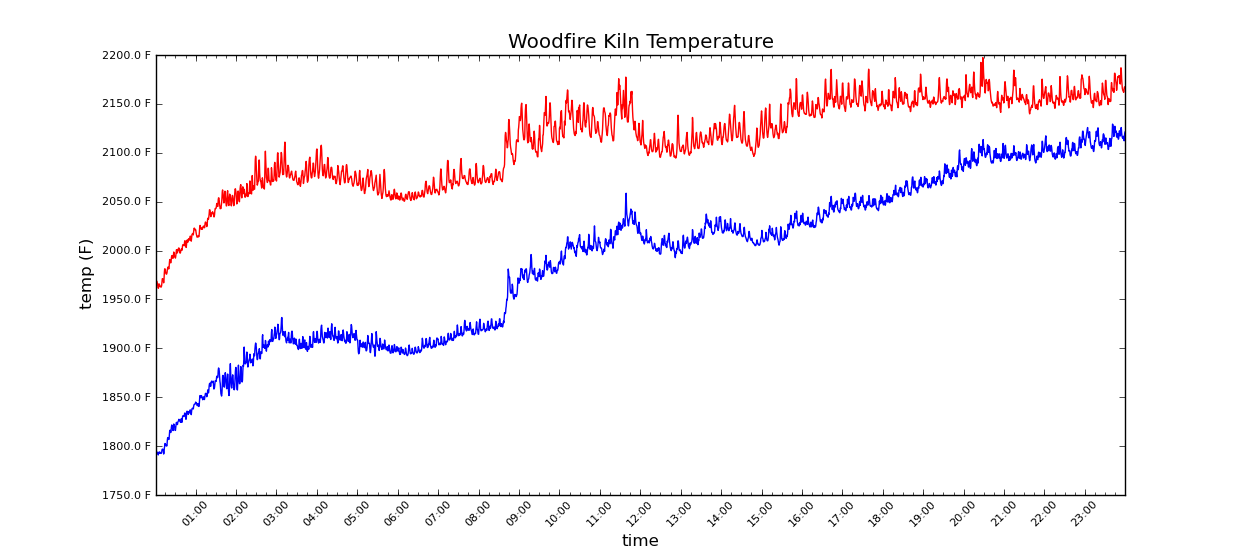
Testing/Anagama_2010_oct/day3.png
