ednspace/PyroLogger/Testing/Anagama_2010_oct/day4.png

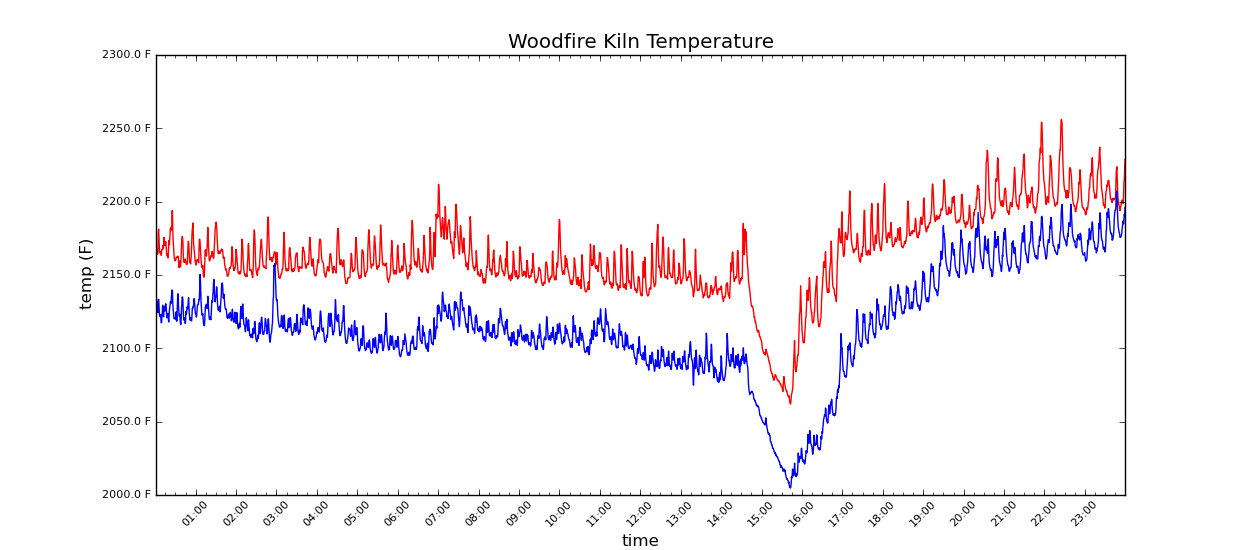
Testing/Anagama_2010_oct/day4.png
