ednspace/PyroLogger/Testing/Anagama_2010_oct/day5.png

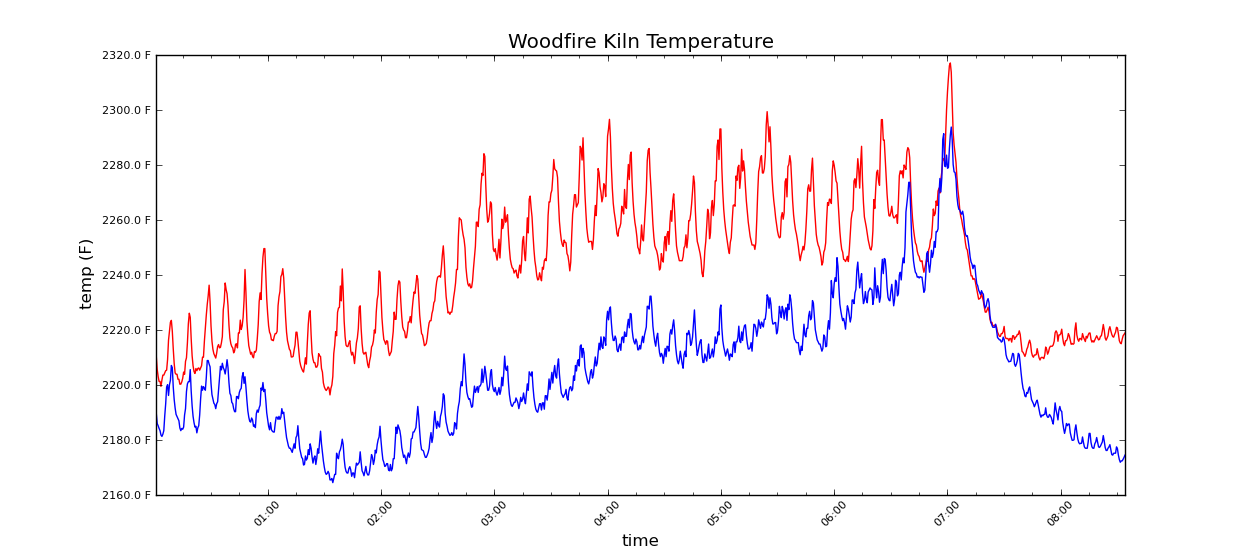
Testing/Anagama_2010_oct/day5.png
