ednspace/PyroLogger/Testing/Testing2014/FirstTestRun.png

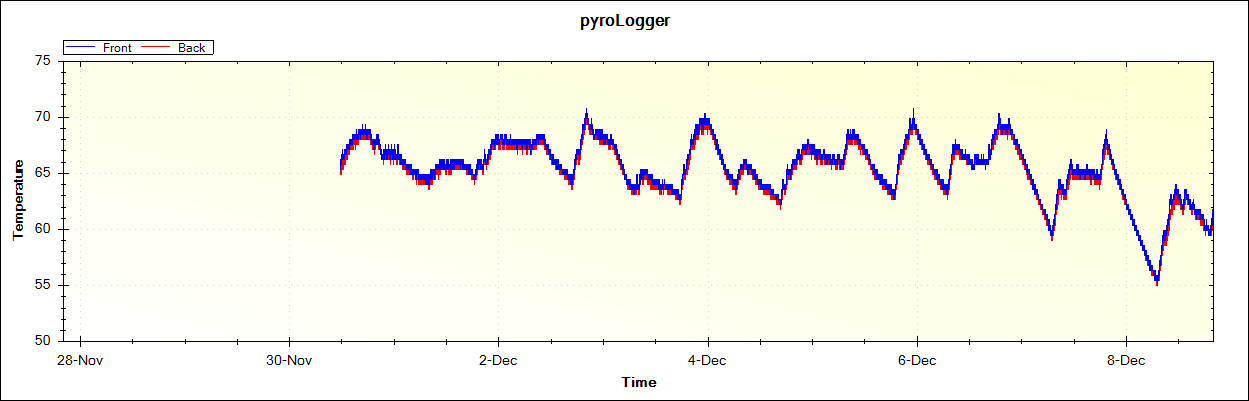
Testing/Testing2014/FirstTestRun.png
