ednspace/PyroLogger/Testing/Testing2014/IncufridgeCoolingOff.png

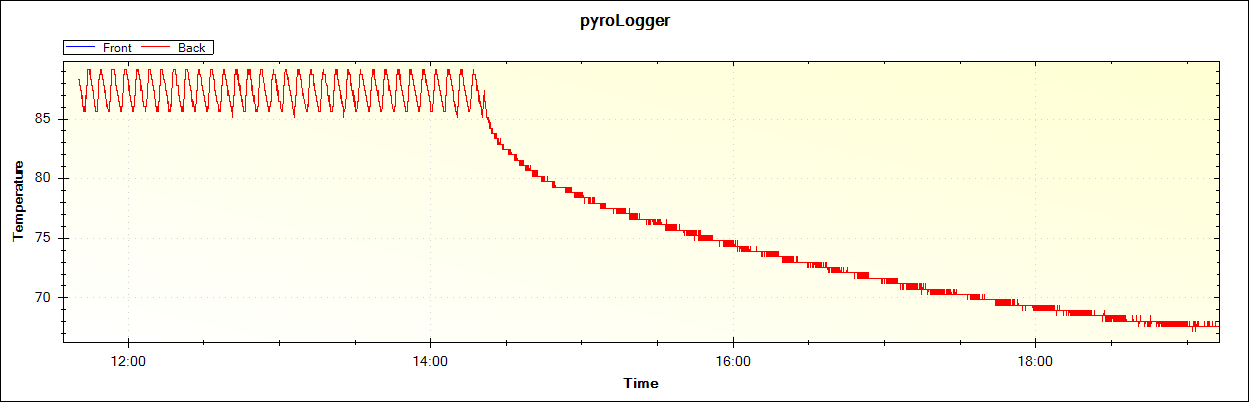
Testing/Testing2014/IncufridgeCoolingOff.png
