ednspace/PyroLogger/Testing/Testing2014/IncufridgeGettingCold.png

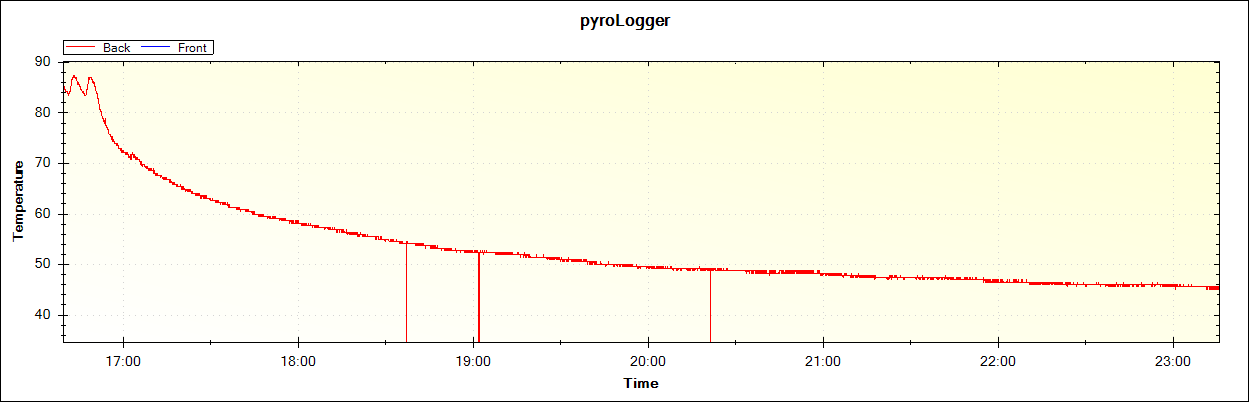
Testing/Testing2014/IncufridgeGettingCold.png
