ednspace/PyroLogger/Testing/Testing2014/TorchBlast.png

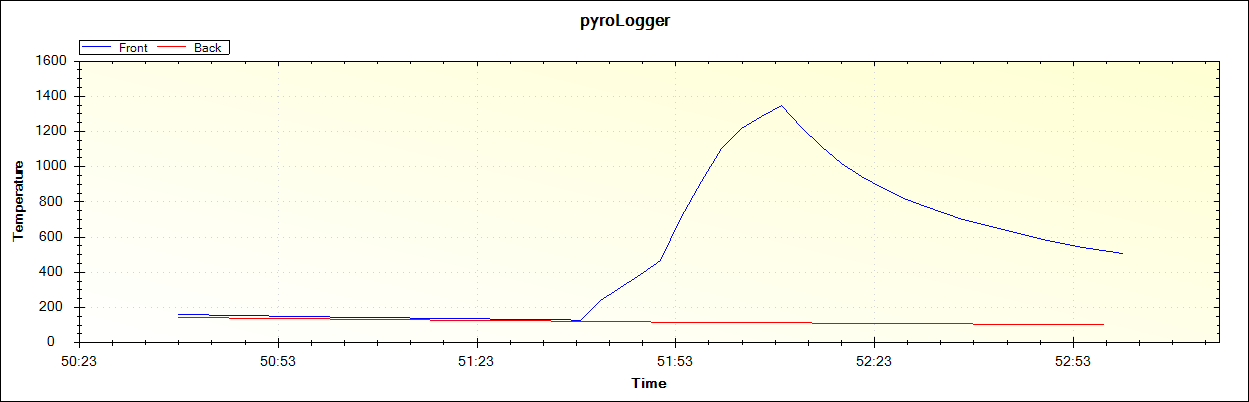
Testing/Testing2014/TorchBlast.png
