ednspace/PyroLogger/Testing/Type_K_error/error.png

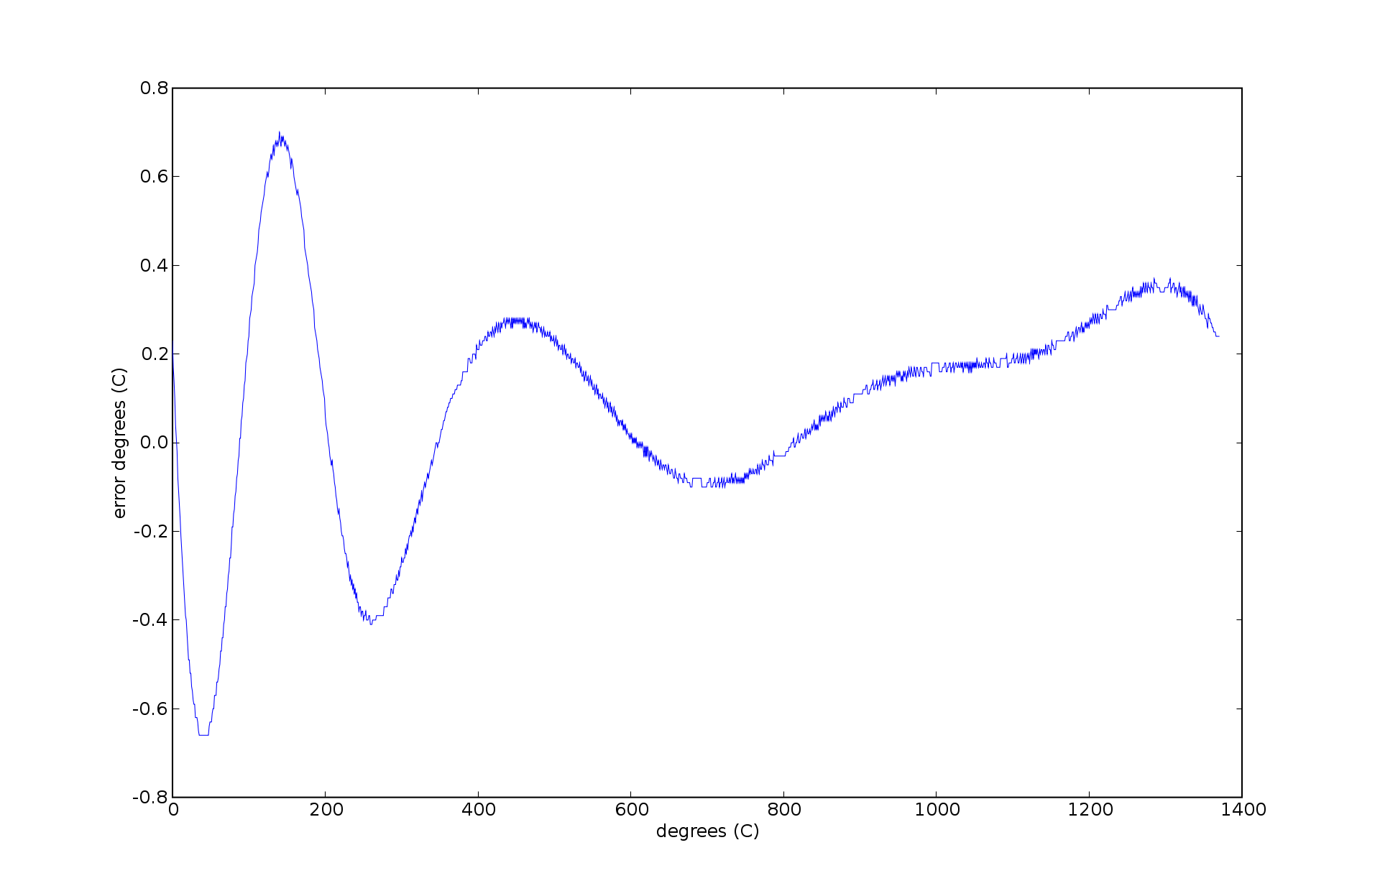
Testing/Type_K_error/error.png
