ednspace/PyroLogger/Research/RJ11-955016449_sd.pdf

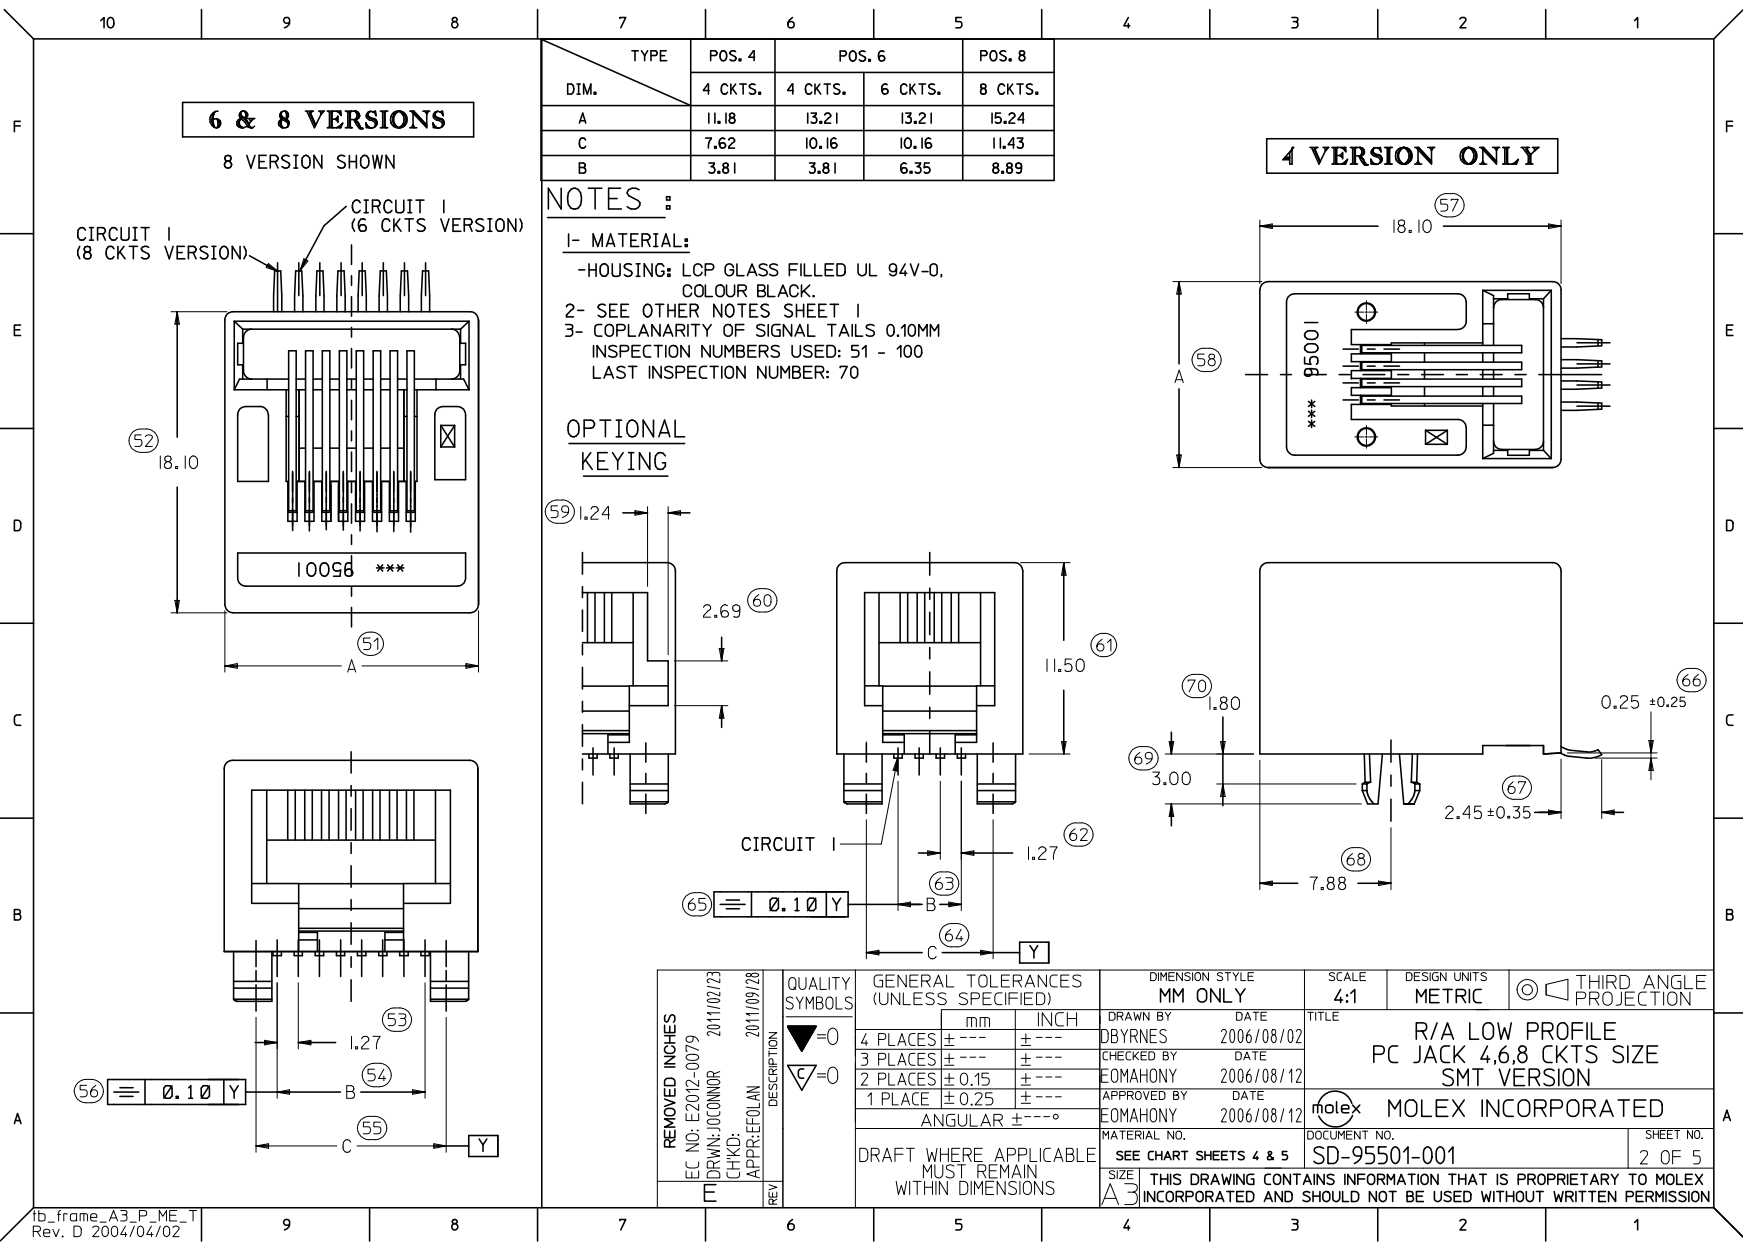
[picture p67: page 1]

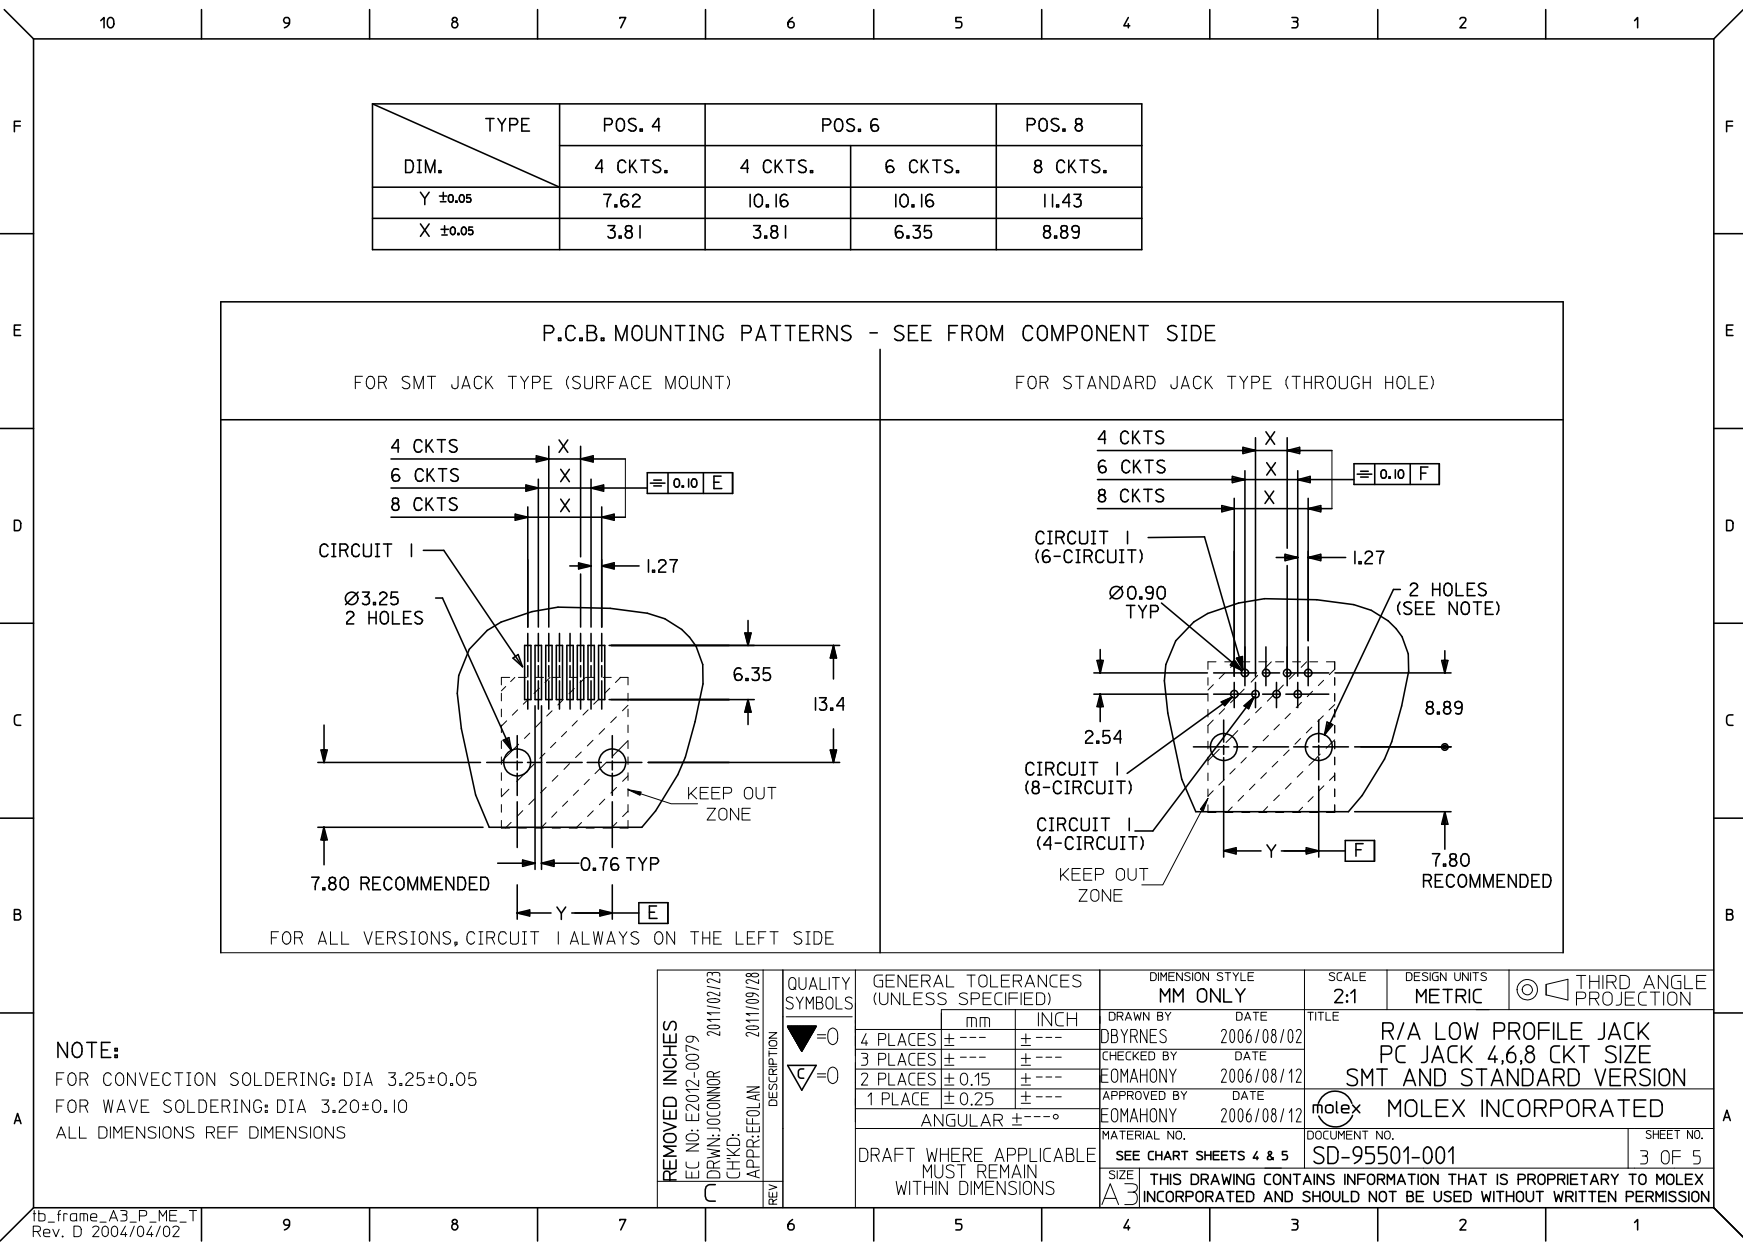
[picture p68: page 2]

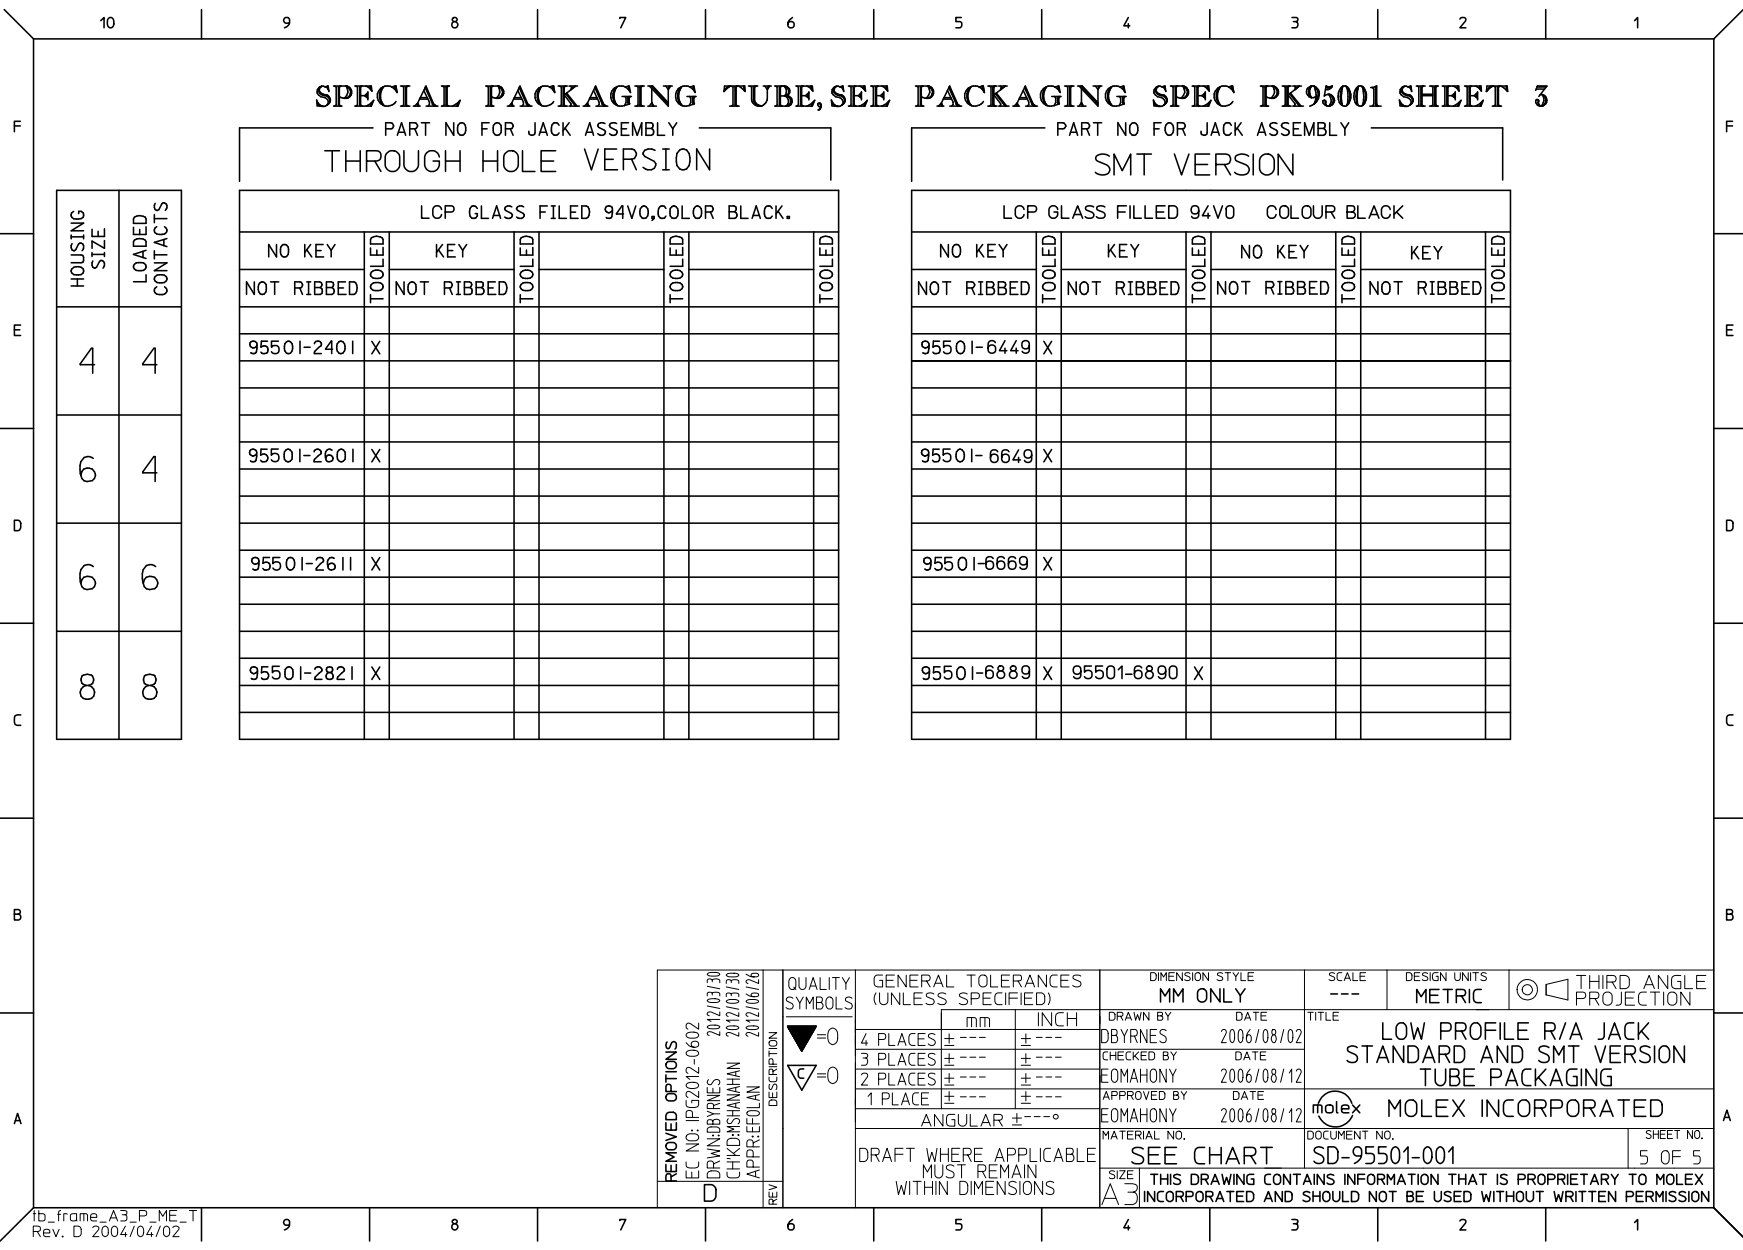
[picture p69: page 3]
